Doly02/nxp-mcxn947-datalogger/application/doc/latex/task__switching_8h.tex

\doxysection{include/task\+\_\+switching.h File Reference}
\hypertarget{task__switching_8h}{}\label{task__switching_8h}\index{include/task\_switching.h@{include/task\_switching.h}}
{\ttfamily \#include "{}usb\+\_\+device\+\_\+dci.\+h"{}}\newline
\doxysubsubsection*{Functions}
\begin{DoxyCompactItemize}
\item 
usb\+\_\+device\+\_\+notification\+\_\+t \mbox{\hyperlink{task__switching_8h_ab4bb1b4063898f52aa390037fc37db81}{USB\+\_\+\+State}} (usb\+\_\+device\+\_\+struct\+\_\+t \texorpdfstring{$\ast$}{*}p\+Device\+Handle)
\begin{DoxyCompactList}\small\item\em Checks If Application USB Is Attached To Digital Data Logger. \end{DoxyCompactList}\end{DoxyCompactItemize}
\doxysubsubsection*{Variables}
\begin{DoxyCompactItemize}
\item 
usb\+\_\+msc\+\_\+struct\+\_\+t \mbox{\hyperlink{task__switching_8h_ae3a33b5a19fe04eeba3ebf4259f74625}{g\+\_\+msc}}
\begin{DoxyCompactList}\small\item\em Mass Storage Descriptor. \end{DoxyCompactList}\end{DoxyCompactItemize}

\doxysubsection{Function Documentation}
\Hypertarget{task__switching_8h_ab4bb1b4063898f52aa390037fc37db81}\index{task\_switching.h@{task\_switching.h}!USB\_State@{USB\_State}}
\index{USB\_State@{USB\_State}!task\_switching.h@{task\_switching.h}}
\doxysubsubsection{\texorpdfstring{USB\_State()}{USB\_State()}}
{\footnotesize\ttfamily \label{task__switching_8h_ab4bb1b4063898f52aa390037fc37db81} 
usb\+\_\+device\+\_\+notification\+\_\+t USB\+\_\+\+State (\begin{DoxyParamCaption}\item[{usb\+\_\+device\+\_\+struct\+\_\+t \texorpdfstring{$\ast$}{*}}]{p\+Device\+Handle}{}\end{DoxyParamCaption})}

Checks If Application USB Is Attached To Digital Data Logger. 

Checks Thru USB OTG (USB On-\/\+To-\/\+Go) SC Register. 
\begin{DoxyParams}[1]{Parameters}
\mbox{\texttt{ in}}  & {\em p\+Device\+Handle} & Pointer to USB Device Handle (e.\+g. Mass Storage Handle).\\
\hline
\end{DoxyParams}
\begin{DoxyReturn}{Returns}
k\+USB\+\_\+\+Device\+Notify\+Attach if USB Is Attached Otherwise Returns k\+USB\+\_\+\+Device\+Notify\+Detach. 
\end{DoxyReturn}

\doxysubsection{Variable Documentation}
\Hypertarget{task__switching_8h_ae3a33b5a19fe04eeba3ebf4259f74625}\index{task\_switching.h@{task\_switching.h}!g\_msc@{g\_msc}}
\index{g\_msc@{g\_msc}!task\_switching.h@{task\_switching.h}}
\doxysubsubsection{\texorpdfstring{g\_msc}{g\_msc}}
{\footnotesize\ttfamily \label{task__switching_8h_ae3a33b5a19fe04eeba3ebf4259f74625} 
usb\+\_\+msc\+\_\+struct\+\_\+t g\+\_\+msc\hspace{0.3cm}{\ttfamily [extern]}}

Mass Storage Descriptor. 

Mass Storage Descriptor.

MISRA Deviation\+: Rule 8.\+4 \mbox{[}Required\mbox{]} Suppress\+: External Object Has Definition Without Prior Declaration in This File. Justification\+: Declaration of \textquotesingle{}g\+\_\+msc\textquotesingle{} is intentionally placed in \textquotesingle{}\doxylink{app__tasks_8h}{app\+\_\+tasks.\+h}\textquotesingle{}, The Current File Only Provides The Definition.
