Doly02/nxp-mcxn947-datalogger/application/doc/latex/temperature_8c.tex

\doxysection{src/temperature.c File Reference}
\hypertarget{temperature_8c}{}\label{temperature_8c}\index{src/temperature.c@{src/temperature.c}}
{\ttfamily \#include $<$led.\+h$>$}\newline
{\ttfamily \#include "{}fsl\+\_\+debug\+\_\+console.\+h"{}}\newline
{\ttfamily \#include "{}fsl\+\_\+ctimer.\+h"{}}\newline
{\ttfamily \#include "{}temperature.\+h"{}}\newline
{\ttfamily \#include "{}defs.\+h"{}}\newline
\doxysubsubsection*{Macros}
\begin{DoxyCompactItemize}
\item 
\#define \mbox{\hyperlink{temperature_8c_afcaf37eb8fb30d41d86b119127cb9368}{LPI2\+C\+\_\+\+TX\+\_\+\+DMA\+\_\+\+CHANNEL}}~0\+UL
\begin{DoxyCompactList}\small\item\em I2C DMA Channel For Transmission. \end{DoxyCompactList}\item 
\#define \mbox{\hyperlink{temperature_8c_a1b99f71e2df43e2f7b57250dba60bc9a}{LPI2\+C\+\_\+\+RX\+\_\+\+DMA\+\_\+\+CHANNEL}}~1UL
\begin{DoxyCompactList}\small\item\em I2C DMA Channel For Reception. \end{DoxyCompactList}\item 
\#define \mbox{\hyperlink{temperature_8c_ae02f1575c21c401c357de6456cb0b472}{LPI2\+C\+\_\+\+TX\+\_\+\+CHANNEL}}~(int32\+\_\+t)k\+Dma1\+Request\+Mux\+Lp\+Flexcomm5\+Tx
\begin{DoxyCompactList}\small\item\em Connection Between DMA Channel 1 and LP\+\_\+\+FLEXCOMM5 Tx. \end{DoxyCompactList}\item 
\#define \mbox{\hyperlink{temperature_8c_aef436e53172ccba5c0370cc9e48d1989}{LPI2\+C\+\_\+\+RX\+\_\+\+EDMA\+\_\+\+CHANNEL}}~(int32\+\_\+t)k\+Dma1\+Request\+Mux\+Lp\+Flexcomm5\+Rx
\begin{DoxyCompactList}\small\item\em Connection Between DMA Channel 1 and LP\+\_\+\+FLEXCOMM5 Rx. \end{DoxyCompactList}\item 
\#define \mbox{\hyperlink{temperature_8c_a886f2dadbf959e761f53d4c0572158e7}{I2\+C\+\_\+\+MASTER\+\_\+\+I2\+C5}}~((LPI2\+C\+\_\+\+Type \texorpdfstring{$\ast$}{*})LPI2\+C5\+\_\+\+BASE)
\begin{DoxyCompactList}\small\item\em Points To I2C Peripheral Unit (Specifically LPI2\+C5 Instance). \end{DoxyCompactList}\item 
\#define \mbox{\hyperlink{temperature_8c_a9c2dd9164220c441449c70bade5baaf1}{P3\+T1755\+\_\+\+ADDR\+\_\+7\+BIT}}~0x48U
\begin{DoxyCompactList}\small\item\em I2C Address of P3\+T1755 Temperature Sensor. \end{DoxyCompactList}\item 
\#define \mbox{\hyperlink{temperature_8c_a31568ea8caf00a3ec699c01652c771d0}{I2\+C\+\_\+\+BAUDRATE}}~100000U
\begin{DoxyCompactList}\small\item\em Desired Baud Rate For I2C. \end{DoxyCompactList}\item 
\#define \mbox{\hyperlink{temperature_8c_a110741ac6782dd7e97d323608505dd1e}{PRINT\+\_\+\+REG\+\_\+\+OUTPUT}}~true
\begin{DoxyCompactList}\small\item\em Enables Printout of P3\+T1755 Register. \end{DoxyCompactList}\item 
\#define \mbox{\hyperlink{temperature_8c_a6c7cd32e1bac137f05e4a752b4ad10af}{BUFF\+\_\+\+SIZE}}~2
\begin{DoxyCompactList}\small\item\em Receive Buffer Size. \end{DoxyCompactList}\item 
\#define \mbox{\hyperlink{temperature_8c_a131b307523cbb7ad0b17a724115a5099}{REGISTER\+\_\+\+TEMPERATURE}}~0x00
\begin{DoxyCompactList}\small\item\em Temperature Register Address of P3\+T1755. \end{DoxyCompactList}\item 
\#define \mbox{\hyperlink{temperature_8c_a46f3492d1abbdaa8919cb57b94343daf}{REGISTER\+\_\+\+CONFIG}}~0x01
\begin{DoxyCompactList}\small\item\em Configuration Register Address of P3\+T1755. \end{DoxyCompactList}\item 
\#define \mbox{\hyperlink{temperature_8c_a31ab751e7975e20c85db034069d4353f}{REGISTER\+\_\+\+THVST}}~0x02
\item 
\#define \mbox{\hyperlink{temperature_8c_a9f4bd4fcf6e33727b5a85c258b8cbe1a}{REGISTER\+\_\+\+TOS}}~0x03
\end{DoxyCompactItemize}
\doxysubsubsection*{Functions}
\begin{DoxyCompactItemize}
\item 
\mbox{\hyperlink{temperature_8c_ab012c2d8730f13da3f0615ca9f93414d}{AT\+\_\+\+NONCACHEABLE\+\_\+\+SECTION}} (static uint8\+\_\+t g\+\_\+a\+Rx\+Buff\+\_\+\+I2\+C5\mbox{[}\mbox{\hyperlink{temperature_8c_a6c7cd32e1bac137f05e4a752b4ad10af}{BUFF\+\_\+\+SIZE}}\mbox{]})
\begin{DoxyCompactList}\small\item\em Reception Buffer. \end{DoxyCompactList}\item 
\mbox{\hyperlink{temperature_8c_a15897befedf315a0700d50b60b6d4bda}{AT\+\_\+\+NONCACHEABLE\+\_\+\+SECTION}} (static lpi2c\+\_\+master\+\_\+edma\+\_\+handle\+\_\+t g\+\_\+\+Edma\+Handle\+\_\+\+I2\+C5)
\begin{DoxyCompactList}\small\item\em e\+DMA Driver Handle Used For Non-\/\+Blocking DMA Transfer. \end{DoxyCompactList}\item 
static void \mbox{\hyperlink{temperature_8c_a038e5a1da8a787ae48b1e279cab6df55}{lpi2c\+\_\+callback}} (LPI2\+C\+\_\+\+Type \texorpdfstring{$\ast$}{*}base, lpi2c\+\_\+master\+\_\+edma\+\_\+handle\+\_\+t \texorpdfstring{$\ast$}{*}handle, status\+\_\+t status, void \texorpdfstring{$\ast$}{*}user\+Data)
\item 
void \mbox{\hyperlink{temperature_8c_a029ce7d1c3ffc8f1d357a6915fb7efc9}{CTIMER0\+\_\+\+IRQHandler}} (void)
\item 
uint8\+\_\+t \mbox{\hyperlink{temperature_8c_ad79223f453fb5cb3b14b0504b78c3b65}{Write}} (uint8\+\_\+t reg\+Address, uint8\+\_\+t val\mbox{[}$\,$\mbox{]})
\begin{DoxyCompactList}\small\item\em I2C Write Function. \end{DoxyCompactList}\item 
uint16\+\_\+t \mbox{\hyperlink{temperature_8c_af7ebaac8aebcb5a7b3147b378d4d1e82}{Read}} (uint8\+\_\+t reg\+Address)
\begin{DoxyCompactList}\small\item\em I2C Read Function. \end{DoxyCompactList}\item 
float \mbox{\hyperlink{temperature_8c_a0b017c2ac439a408d7b0d2bb07c2c3af}{TMP\+\_\+\+Get\+Temperature}} (void)
\begin{DoxyCompactList}\small\item\em Gets Temperature From On-\/\+Board P3\+T1755 Temperature Sensor. \end{DoxyCompactList}\item 
uint8\+\_\+t \mbox{\hyperlink{temperature_8c_a147cb7fa3ec99aa1038a20fd3d5ed0c3}{TMP\+\_\+\+Init}} (void)
\begin{DoxyCompactList}\small\item\em Initialize On-\/\+Board P3\+T1755 Temperature Sensor. \end{DoxyCompactList}\end{DoxyCompactItemize}
\doxysubsubsection*{Variables}
\begin{DoxyCompactItemize}
\item 
static edma\+\_\+handle\+\_\+t \mbox{\hyperlink{temperature_8c_a50fdd2b8d8084e9a4e600ae8af2f258a}{g\+\_\+\+Edma\+Tx\+Handle\+\_\+\+I2\+C5}}
\begin{DoxyCompactList}\small\item\em Tx e\+DMA Handle. \end{DoxyCompactList}\item 
static edma\+\_\+handle\+\_\+t \mbox{\hyperlink{temperature_8c_a776091829eca10175ea2ede27a31c45b}{g\+\_\+\+Edma\+Rx\+Handle\+\_\+\+I2\+C5}}
\begin{DoxyCompactList}\small\item\em Rx e\+DMA Handle. \end{DoxyCompactList}\item 
static volatile bool \mbox{\hyperlink{temperature_8c_a5c2a41bb43d5c3f97eaeff90195f16e0}{g\+\_\+b\+Completion\+Flag\+\_\+\+I2\+C5}} = false
\begin{DoxyCompactList}\small\item\em Flag Indicating Whether The Transfer Has Finished. \end{DoxyCompactList}\item 
static lpi2c\+\_\+master\+\_\+transfer\+\_\+t \mbox{\hyperlink{temperature_8c_a04223a52c21e3c74a057039cc4859680}{g\+\_\+\+Xfer\+\_\+\+I2\+C5}} = \{0\}
\end{DoxyCompactItemize}

\doxysubsection{Macro Definition Documentation}
\Hypertarget{temperature_8c_a6c7cd32e1bac137f05e4a752b4ad10af}\index{temperature.c@{temperature.c}!BUFF\_SIZE@{BUFF\_SIZE}}
\index{BUFF\_SIZE@{BUFF\_SIZE}!temperature.c@{temperature.c}}
\doxysubsubsection{\texorpdfstring{BUFF\_SIZE}{BUFF\_SIZE}}
{\footnotesize\ttfamily \label{temperature_8c_a6c7cd32e1bac137f05e4a752b4ad10af} 
\#define BUFF\+\_\+\+SIZE~2}

Receive Buffer Size. 

\Hypertarget{temperature_8c_a31568ea8caf00a3ec699c01652c771d0}\index{temperature.c@{temperature.c}!I2C\_BAUDRATE@{I2C\_BAUDRATE}}
\index{I2C\_BAUDRATE@{I2C\_BAUDRATE}!temperature.c@{temperature.c}}
\doxysubsubsection{\texorpdfstring{I2C\_BAUDRATE}{I2C\_BAUDRATE}}
{\footnotesize\ttfamily \label{temperature_8c_a31568ea8caf00a3ec699c01652c771d0} 
\#define I2\+C\+\_\+\+BAUDRATE~100000U}

Desired Baud Rate For I2C. 

Frequency -\/ 100k\+Hz. \Hypertarget{temperature_8c_a886f2dadbf959e761f53d4c0572158e7}\index{temperature.c@{temperature.c}!I2C\_MASTER\_I2C5@{I2C\_MASTER\_I2C5}}
\index{I2C\_MASTER\_I2C5@{I2C\_MASTER\_I2C5}!temperature.c@{temperature.c}}
\doxysubsubsection{\texorpdfstring{I2C\_MASTER\_I2C5}{I2C\_MASTER\_I2C5}}
{\footnotesize\ttfamily \label{temperature_8c_a886f2dadbf959e761f53d4c0572158e7} 
\#define I2\+C\+\_\+\+MASTER\+\_\+\+I2\+C5~((LPI2\+C\+\_\+\+Type \texorpdfstring{$\ast$}{*})LPI2\+C5\+\_\+\+BASE)}

Points To I2C Peripheral Unit (Specifically LPI2\+C5 Instance). 

\Hypertarget{temperature_8c_a1b99f71e2df43e2f7b57250dba60bc9a}\index{temperature.c@{temperature.c}!LPI2C\_RX\_DMA\_CHANNEL@{LPI2C\_RX\_DMA\_CHANNEL}}
\index{LPI2C\_RX\_DMA\_CHANNEL@{LPI2C\_RX\_DMA\_CHANNEL}!temperature.c@{temperature.c}}
\doxysubsubsection{\texorpdfstring{LPI2C\_RX\_DMA\_CHANNEL}{LPI2C\_RX\_DMA\_CHANNEL}}
{\footnotesize\ttfamily \label{temperature_8c_a1b99f71e2df43e2f7b57250dba60bc9a} 
\#define LPI2\+C\+\_\+\+RX\+\_\+\+DMA\+\_\+\+CHANNEL~1UL}

I2C DMA Channel For Reception. 

\Hypertarget{temperature_8c_aef436e53172ccba5c0370cc9e48d1989}\index{temperature.c@{temperature.c}!LPI2C\_RX\_EDMA\_CHANNEL@{LPI2C\_RX\_EDMA\_CHANNEL}}
\index{LPI2C\_RX\_EDMA\_CHANNEL@{LPI2C\_RX\_EDMA\_CHANNEL}!temperature.c@{temperature.c}}
\doxysubsubsection{\texorpdfstring{LPI2C\_RX\_EDMA\_CHANNEL}{LPI2C\_RX\_EDMA\_CHANNEL}}
{\footnotesize\ttfamily \label{temperature_8c_aef436e53172ccba5c0370cc9e48d1989} 
\#define LPI2\+C\+\_\+\+RX\+\_\+\+EDMA\+\_\+\+CHANNEL~(int32\+\_\+t)k\+Dma1\+Request\+Mux\+Lp\+Flexcomm5\+Rx}

Connection Between DMA Channel 1 and LP\+\_\+\+FLEXCOMM5 Rx. 

\Hypertarget{temperature_8c_ae02f1575c21c401c357de6456cb0b472}\index{temperature.c@{temperature.c}!LPI2C\_TX\_CHANNEL@{LPI2C\_TX\_CHANNEL}}
\index{LPI2C\_TX\_CHANNEL@{LPI2C\_TX\_CHANNEL}!temperature.c@{temperature.c}}
\doxysubsubsection{\texorpdfstring{LPI2C\_TX\_CHANNEL}{LPI2C\_TX\_CHANNEL}}
{\footnotesize\ttfamily \label{temperature_8c_ae02f1575c21c401c357de6456cb0b472} 
\#define LPI2\+C\+\_\+\+TX\+\_\+\+CHANNEL~(int32\+\_\+t)k\+Dma1\+Request\+Mux\+Lp\+Flexcomm5\+Tx}

Connection Between DMA Channel 1 and LP\+\_\+\+FLEXCOMM5 Tx. 

\Hypertarget{temperature_8c_afcaf37eb8fb30d41d86b119127cb9368}\index{temperature.c@{temperature.c}!LPI2C\_TX\_DMA\_CHANNEL@{LPI2C\_TX\_DMA\_CHANNEL}}
\index{LPI2C\_TX\_DMA\_CHANNEL@{LPI2C\_TX\_DMA\_CHANNEL}!temperature.c@{temperature.c}}
\doxysubsubsection{\texorpdfstring{LPI2C\_TX\_DMA\_CHANNEL}{LPI2C\_TX\_DMA\_CHANNEL}}
{\footnotesize\ttfamily \label{temperature_8c_afcaf37eb8fb30d41d86b119127cb9368} 
\#define LPI2\+C\+\_\+\+TX\+\_\+\+DMA\+\_\+\+CHANNEL~0\+UL}

I2C DMA Channel For Transmission. 

\Hypertarget{temperature_8c_a9c2dd9164220c441449c70bade5baaf1}\index{temperature.c@{temperature.c}!P3T1755\_ADDR\_7BIT@{P3T1755\_ADDR\_7BIT}}
\index{P3T1755\_ADDR\_7BIT@{P3T1755\_ADDR\_7BIT}!temperature.c@{temperature.c}}
\doxysubsubsection{\texorpdfstring{P3T1755\_ADDR\_7BIT}{P3T1755\_ADDR\_7BIT}}
{\footnotesize\ttfamily \label{temperature_8c_a9c2dd9164220c441449c70bade5baaf1} 
\#define P3\+T1755\+\_\+\+ADDR\+\_\+7\+BIT~0x48U}

I2C Address of P3\+T1755 Temperature Sensor. 

\Hypertarget{temperature_8c_a110741ac6782dd7e97d323608505dd1e}\index{temperature.c@{temperature.c}!PRINT\_REG\_OUTPUT@{PRINT\_REG\_OUTPUT}}
\index{PRINT\_REG\_OUTPUT@{PRINT\_REG\_OUTPUT}!temperature.c@{temperature.c}}
\doxysubsubsection{\texorpdfstring{PRINT\_REG\_OUTPUT}{PRINT\_REG\_OUTPUT}}
{\footnotesize\ttfamily \label{temperature_8c_a110741ac6782dd7e97d323608505dd1e} 
\#define PRINT\+\_\+\+REG\+\_\+\+OUTPUT~true}

Enables Printout of P3\+T1755 Register. 

\Hypertarget{temperature_8c_a46f3492d1abbdaa8919cb57b94343daf}\index{temperature.c@{temperature.c}!REGISTER\_CONFIG@{REGISTER\_CONFIG}}
\index{REGISTER\_CONFIG@{REGISTER\_CONFIG}!temperature.c@{temperature.c}}
\doxysubsubsection{\texorpdfstring{REGISTER\_CONFIG}{REGISTER\_CONFIG}}
{\footnotesize\ttfamily \label{temperature_8c_a46f3492d1abbdaa8919cb57b94343daf} 
\#define REGISTER\+\_\+\+CONFIG~0x01}

Configuration Register Address of P3\+T1755. 

\Hypertarget{temperature_8c_a131b307523cbb7ad0b17a724115a5099}\index{temperature.c@{temperature.c}!REGISTER\_TEMPERATURE@{REGISTER\_TEMPERATURE}}
\index{REGISTER\_TEMPERATURE@{REGISTER\_TEMPERATURE}!temperature.c@{temperature.c}}
\doxysubsubsection{\texorpdfstring{REGISTER\_TEMPERATURE}{REGISTER\_TEMPERATURE}}
{\footnotesize\ttfamily \label{temperature_8c_a131b307523cbb7ad0b17a724115a5099} 
\#define REGISTER\+\_\+\+TEMPERATURE~0x00}

Temperature Register Address of P3\+T1755. 

\Hypertarget{temperature_8c_a31ab751e7975e20c85db034069d4353f}\index{temperature.c@{temperature.c}!REGISTER\_THVST@{REGISTER\_THVST}}
\index{REGISTER\_THVST@{REGISTER\_THVST}!temperature.c@{temperature.c}}
\doxysubsubsection{\texorpdfstring{REGISTER\_THVST}{REGISTER\_THVST}}
{\footnotesize\ttfamily \label{temperature_8c_a31ab751e7975e20c85db034069d4353f} 
\#define REGISTER\+\_\+\+THVST~0x02}

\Hypertarget{temperature_8c_a9f4bd4fcf6e33727b5a85c258b8cbe1a}\index{temperature.c@{temperature.c}!REGISTER\_TOS@{REGISTER\_TOS}}
\index{REGISTER\_TOS@{REGISTER\_TOS}!temperature.c@{temperature.c}}
\doxysubsubsection{\texorpdfstring{REGISTER\_TOS}{REGISTER\_TOS}}
{\footnotesize\ttfamily \label{temperature_8c_a9f4bd4fcf6e33727b5a85c258b8cbe1a} 
\#define REGISTER\+\_\+\+TOS~0x03}

\doxysubsection{Function Documentation}
\Hypertarget{temperature_8c_a15897befedf315a0700d50b60b6d4bda}\index{temperature.c@{temperature.c}!AT\_NONCACHEABLE\_SECTION@{AT\_NONCACHEABLE\_SECTION}}
\index{AT\_NONCACHEABLE\_SECTION@{AT\_NONCACHEABLE\_SECTION}!temperature.c@{temperature.c}}
\doxysubsubsection{\texorpdfstring{AT\_NONCACHEABLE\_SECTION()}{AT\_NONCACHEABLE\_SECTION()}\hspace{0.1cm}{\footnotesize\ttfamily [1/2]}}
{\footnotesize\ttfamily \label{temperature_8c_a15897befedf315a0700d50b60b6d4bda} 
AT\+\_\+\+NONCACHEABLE\+\_\+\+SECTION (\begin{DoxyParamCaption}\item[{static lpi2c\+\_\+master\+\_\+edma\+\_\+handle\+\_\+t}]{g\+\_\+\+Edma\+Handle\+\_\+\+I2\+C5}{}\end{DoxyParamCaption})}

e\+DMA Driver Handle Used For Non-\/\+Blocking DMA Transfer. 

\Hypertarget{temperature_8c_ab012c2d8730f13da3f0615ca9f93414d}\index{temperature.c@{temperature.c}!AT\_NONCACHEABLE\_SECTION@{AT\_NONCACHEABLE\_SECTION}}
\index{AT\_NONCACHEABLE\_SECTION@{AT\_NONCACHEABLE\_SECTION}!temperature.c@{temperature.c}}
\doxysubsubsection{\texorpdfstring{AT\_NONCACHEABLE\_SECTION()}{AT\_NONCACHEABLE\_SECTION()}\hspace{0.1cm}{\footnotesize\ttfamily [2/2]}}
{\footnotesize\ttfamily \label{temperature_8c_ab012c2d8730f13da3f0615ca9f93414d} 
AT\+\_\+\+NONCACHEABLE\+\_\+\+SECTION (\begin{DoxyParamCaption}\item[{static uint8\+\_\+t}]{g\+\_\+a\+Rx\+Buff\+\_\+\+I2\+C5}{\mbox{[}\+BUFF\+\_\+\+SIZE\mbox{]}}\end{DoxyParamCaption})}

Reception Buffer. 

Must Be In Non-\/\+Cacheable Memory Due To Usage of DMA. \Hypertarget{temperature_8c_a029ce7d1c3ffc8f1d357a6915fb7efc9}\index{temperature.c@{temperature.c}!CTIMER0\_IRQHandler@{CTIMER0\_IRQHandler}}
\index{CTIMER0\_IRQHandler@{CTIMER0\_IRQHandler}!temperature.c@{temperature.c}}
\doxysubsubsection{\texorpdfstring{CTIMER0\_IRQHandler()}{CTIMER0\_IRQHandler()}}
{\footnotesize\ttfamily \label{temperature_8c_a029ce7d1c3ffc8f1d357a6915fb7efc9} 
void CTIMER0\+\_\+\+IRQHandler (\begin{DoxyParamCaption}\item[{void}]{}{}\end{DoxyParamCaption})}

\Hypertarget{temperature_8c_a038e5a1da8a787ae48b1e279cab6df55}\index{temperature.c@{temperature.c}!lpi2c\_callback@{lpi2c\_callback}}
\index{lpi2c\_callback@{lpi2c\_callback}!temperature.c@{temperature.c}}
\doxysubsubsection{\texorpdfstring{lpi2c\_callback()}{lpi2c\_callback()}}
{\footnotesize\ttfamily \label{temperature_8c_a038e5a1da8a787ae48b1e279cab6df55} 
static void lpi2c\+\_\+callback (\begin{DoxyParamCaption}\item[{LPI2\+C\+\_\+\+Type \texorpdfstring{$\ast$}{*}}]{base}{, }\item[{lpi2c\+\_\+master\+\_\+edma\+\_\+handle\+\_\+t \texorpdfstring{$\ast$}{*}}]{handle}{, }\item[{status\+\_\+t}]{status}{, }\item[{void \texorpdfstring{$\ast$}{*}}]{user\+Data}{}\end{DoxyParamCaption})\hspace{0.3cm}{\ttfamily [static]}}

\Hypertarget{temperature_8c_af7ebaac8aebcb5a7b3147b378d4d1e82}\index{temperature.c@{temperature.c}!Read@{Read}}
\index{Read@{Read}!temperature.c@{temperature.c}}
\doxysubsubsection{\texorpdfstring{Read()}{Read()}}
{\footnotesize\ttfamily \label{temperature_8c_af7ebaac8aebcb5a7b3147b378d4d1e82} 
uint16\+\_\+t Read (\begin{DoxyParamCaption}\item[{uint8\+\_\+t}]{reg\+Address}{}\end{DoxyParamCaption})}

I2C Read Function. 

\begin{DoxyParams}[1]{Parameters}
\mbox{\texttt{ in}}  & {\em reg\+Address} & Address of The Register From Which The Reading Will Take Place.\\
\hline
\end{DoxyParams}

\begin{DoxyRetVals}{Return values}
{\em Returns} & The Read Value From The Registry. \\
\hline
\end{DoxyRetVals}
\Hypertarget{temperature_8c_a0b017c2ac439a408d7b0d2bb07c2c3af}\index{temperature.c@{temperature.c}!TMP\_GetTemperature@{TMP\_GetTemperature}}
\index{TMP\_GetTemperature@{TMP\_GetTemperature}!temperature.c@{temperature.c}}
\doxysubsubsection{\texorpdfstring{TMP\_GetTemperature()}{TMP\_GetTemperature()}}
{\footnotesize\ttfamily \label{temperature_8c_a0b017c2ac439a408d7b0d2bb07c2c3af} 
float TMP\+\_\+\+Get\+Temperature (\begin{DoxyParamCaption}\item[{void}]{}{}\end{DoxyParamCaption})}

Gets Temperature From On-\/\+Board P3\+T1755 Temperature Sensor. 

\begin{DoxyRetVals}{Return values}
{\em Returns} & Temperature As Float Number. \\
\hline
\end{DoxyRetVals}
\Hypertarget{temperature_8c_a147cb7fa3ec99aa1038a20fd3d5ed0c3}\index{temperature.c@{temperature.c}!TMP\_Init@{TMP\_Init}}
\index{TMP\_Init@{TMP\_Init}!temperature.c@{temperature.c}}
\doxysubsubsection{\texorpdfstring{TMP\_Init()}{TMP\_Init()}}
{\footnotesize\ttfamily \label{temperature_8c_a147cb7fa3ec99aa1038a20fd3d5ed0c3} 
uint8\+\_\+t TMP\+\_\+\+Init (\begin{DoxyParamCaption}\item[{void}]{}{}\end{DoxyParamCaption})}

Initialize On-\/\+Board P3\+T1755 Temperature Sensor. 

\Hypertarget{temperature_8c_ad79223f453fb5cb3b14b0504b78c3b65}\index{temperature.c@{temperature.c}!Write@{Write}}
\index{Write@{Write}!temperature.c@{temperature.c}}
\doxysubsubsection{\texorpdfstring{Write()}{Write()}}
{\footnotesize\ttfamily \label{temperature_8c_ad79223f453fb5cb3b14b0504b78c3b65} 
uint8\+\_\+t Write (\begin{DoxyParamCaption}\item[{uint8\+\_\+t}]{reg\+Address}{, }\item[{uint8\+\_\+t}]{val}{\mbox{[}$\,$\mbox{]}}\end{DoxyParamCaption})}

I2C Write Function. 

\begin{DoxyParams}[1]{Parameters}
\mbox{\texttt{ in}}  & {\em reg\+Address} & Address of The Register To Be Written To. \\
\hline
\mbox{\texttt{ in}}  & {\em val} & Array of Values To Be Written To The Register.\\
\hline
\end{DoxyParams}

\begin{DoxyRetVals}{Return values}
{\em If} & The Write Succeeds, Returns 0. \\
\hline
\end{DoxyRetVals}

\doxysubsection{Variable Documentation}
\Hypertarget{temperature_8c_a5c2a41bb43d5c3f97eaeff90195f16e0}\index{temperature.c@{temperature.c}!g\_bCompletionFlag\_I2C5@{g\_bCompletionFlag\_I2C5}}
\index{g\_bCompletionFlag\_I2C5@{g\_bCompletionFlag\_I2C5}!temperature.c@{temperature.c}}
\doxysubsubsection{\texorpdfstring{g\_bCompletionFlag\_I2C5}{g\_bCompletionFlag\_I2C5}}
{\footnotesize\ttfamily \label{temperature_8c_a5c2a41bb43d5c3f97eaeff90195f16e0} 
volatile bool g\+\_\+b\+Completion\+Flag\+\_\+\+I2\+C5 = false\hspace{0.3cm}{\ttfamily [static]}}

Flag Indicating Whether The Transfer Has Finished. 

\Hypertarget{temperature_8c_a776091829eca10175ea2ede27a31c45b}\index{temperature.c@{temperature.c}!g\_EdmaRxHandle\_I2C5@{g\_EdmaRxHandle\_I2C5}}
\index{g\_EdmaRxHandle\_I2C5@{g\_EdmaRxHandle\_I2C5}!temperature.c@{temperature.c}}
\doxysubsubsection{\texorpdfstring{g\_EdmaRxHandle\_I2C5}{g\_EdmaRxHandle\_I2C5}}
{\footnotesize\ttfamily \label{temperature_8c_a776091829eca10175ea2ede27a31c45b} 
edma\+\_\+handle\+\_\+t g\+\_\+\+Edma\+Rx\+Handle\+\_\+\+I2\+C5\hspace{0.3cm}{\ttfamily [static]}}

Rx e\+DMA Handle. 

\Hypertarget{temperature_8c_a50fdd2b8d8084e9a4e600ae8af2f258a}\index{temperature.c@{temperature.c}!g\_EdmaTxHandle\_I2C5@{g\_EdmaTxHandle\_I2C5}}
\index{g\_EdmaTxHandle\_I2C5@{g\_EdmaTxHandle\_I2C5}!temperature.c@{temperature.c}}
\doxysubsubsection{\texorpdfstring{g\_EdmaTxHandle\_I2C5}{g\_EdmaTxHandle\_I2C5}}
{\footnotesize\ttfamily \label{temperature_8c_a50fdd2b8d8084e9a4e600ae8af2f258a} 
edma\+\_\+handle\+\_\+t g\+\_\+\+Edma\+Tx\+Handle\+\_\+\+I2\+C5\hspace{0.3cm}{\ttfamily [static]}}

Tx e\+DMA Handle. 

\Hypertarget{temperature_8c_a04223a52c21e3c74a057039cc4859680}\index{temperature.c@{temperature.c}!g\_Xfer\_I2C5@{g\_Xfer\_I2C5}}
\index{g\_Xfer\_I2C5@{g\_Xfer\_I2C5}!temperature.c@{temperature.c}}
\doxysubsubsection{\texorpdfstring{g\_Xfer\_I2C5}{g\_Xfer\_I2C5}}
{\footnotesize\ttfamily \label{temperature_8c_a04223a52c21e3c74a057039cc4859680} 
lpi2c\+\_\+master\+\_\+transfer\+\_\+t g\+\_\+\+Xfer\+\_\+\+I2\+C5 = \{0\}\hspace{0.3cm}{\ttfamily [static]}}
