Doly02/nxp-mcxn947-datalogger/application/doc/latex/uart_8h_source.tex

\doxysection{uart.\+h}
\hypertarget{uart_8h_source}{}\label{uart_8h_source}\index{include/uart.h@{include/uart.h}}
\mbox{\hyperlink{uart_8h}{Go to the documentation of this file.}}
\begin{DoxyCode}{0}
\DoxyCodeLine{00001\ \textcolor{comment}{/******************************}}
\DoxyCodeLine{00002\ \textcolor{comment}{\ *\ \ Project:\ \ \ \ \ \ \ \ NXP\ MCXN947\ Datalogger}}
\DoxyCodeLine{00003\ \textcolor{comment}{\ *\ \ File\ Name:\ \ \ \ \ \ uart.h}}
\DoxyCodeLine{00004\ \textcolor{comment}{\ *\ \ Author:\ \ \ \ \ \ \ \ \ Tomas\ Dolak}}
\DoxyCodeLine{00005\ \textcolor{comment}{\ *\ \ Date:\ \ \ \ \ \ \ \ \ \ \ 25.11.2024}}
\DoxyCodeLine{00006\ \textcolor{comment}{\ *\ \ Description:\ \ \ \ Header\ File\ For\ The\ UART\ Peripheral\ Support.}}
\DoxyCodeLine{00007\ \textcolor{comment}{\ *}}
\DoxyCodeLine{00008\ \textcolor{comment}{\ *\ ****************************/}}
\DoxyCodeLine{00009\ }
\DoxyCodeLine{00010\ \textcolor{comment}{/******************************}}
\DoxyCodeLine{00011\ \textcolor{comment}{\ *\ \ @package\ \ \ \ \ \ \ \ NXP\ MCXN947\ Datalogger}}
\DoxyCodeLine{00012\ \textcolor{comment}{\ *\ \ @file\ \ \ \ \ \ \ \ \ \ \ uart.h}}
\DoxyCodeLine{00013\ \textcolor{comment}{\ *\ \ @author\ \ \ \ \ \ \ \ \ Tomas\ Dolak}}
\DoxyCodeLine{00014\ \textcolor{comment}{\ *\ \ @date\ \ \ \ \ \ \ \ \ \ \ 25.11.2024}}
\DoxyCodeLine{00015\ \textcolor{comment}{\ *\ \ @brief\ \ \ \ \ \ \ \ \ \ Header\ File\ For\ The\ UART\ Peripheral\ Support.}}
\DoxyCodeLine{00016\ \textcolor{comment}{\ *\ ****************************/}}
\DoxyCodeLine{00017\ }
\DoxyCodeLine{00018\ \textcolor{preprocessor}{\#ifndef\ UART\_H\_}}
\DoxyCodeLine{00019\ \textcolor{preprocessor}{\#define\ UART\_H\_}}
\DoxyCodeLine{00020\ }
\DoxyCodeLine{00021\ \textcolor{comment}{/*******************************************************************************}}
\DoxyCodeLine{00022\ \textcolor{comment}{\ *\ Includes}}
\DoxyCodeLine{00023\ \textcolor{comment}{\ ******************************************************************************/}}
\DoxyCodeLine{00024\ \textcolor{preprocessor}{\#include\ "{}pin\_mux.h"{}}}
\DoxyCodeLine{00025\ \textcolor{preprocessor}{\#include\ "{}clock\_config.h"{}}}
\DoxyCodeLine{00026\ \textcolor{preprocessor}{\#include\ "{}board.h"{}}}
\DoxyCodeLine{00027\ \textcolor{preprocessor}{\#include\ "{}fsl\_lpuart.h"{}}}
\DoxyCodeLine{00028\ }
\DoxyCodeLine{00029\ \textcolor{preprocessor}{\#include\ "{}fsl\_debug\_console.h"{}}}
\DoxyCodeLine{00030\ \textcolor{preprocessor}{\#include\ "{}fsl\_clock.h"{}}}
\DoxyCodeLine{00031\ \textcolor{comment}{/*******************************************************************************}}
\DoxyCodeLine{00032\ \textcolor{comment}{\ *\ Definitions}}
\DoxyCodeLine{00033\ \textcolor{comment}{\ ******************************************************************************/}}
\DoxyCodeLine{00037\ \textcolor{preprocessor}{\#define\ LPUART3\_CLK\_FREQ\ \ \ CLOCK\_GetLPFlexCommClkFreq(3u)}}
\DoxyCodeLine{00038\ }
\DoxyCodeLine{00039\ }
\DoxyCodeLine{00040\ \textcolor{comment}{/*******************************************************************************}}
\DoxyCodeLine{00041\ \textcolor{comment}{\ *\ Declarations}}
\DoxyCodeLine{00042\ \textcolor{comment}{\ ******************************************************************************/}}
\DoxyCodeLine{00043\ }
\DoxyCodeLine{00047\ \textcolor{keywordtype}{void}\ \mbox{\hyperlink{uart_8h_ad6f6f2234554d7faf55db52b66f45bc5}{UART\_Init}}(uint32\_t\ baudrate);}
\DoxyCodeLine{00048\ }
\DoxyCodeLine{00054\ \textcolor{keywordtype}{void}\ \mbox{\hyperlink{uart_8h_a6ee3953aba06a9d3e1695bb3ba147c18}{UART\_Print}}(uint8\_t\ ch);}
\DoxyCodeLine{00055\ }
\DoxyCodeLine{00059\ \textcolor{keywordtype}{void}\ \mbox{\hyperlink{uart_8h_ae2d34afb9a8bd33f0229eb6b34c57df2}{UART\_Enable}}(\textcolor{keywordtype}{void});}
\DoxyCodeLine{00060\ }
\DoxyCodeLine{00064\ \textcolor{keywordtype}{void}\ \mbox{\hyperlink{uart_8h_a76482cf7e9eb69dba68afd26b53b7f37}{UART\_Disable}}(\textcolor{keywordtype}{void});}
\DoxyCodeLine{00065\ }
\DoxyCodeLine{00070\ \textcolor{keywordtype}{void}\ \mbox{\hyperlink{uart_8h_a28f24a41744d2b956de47ae6318d9c05}{UART\_Deinit}}(\textcolor{keywordtype}{void});}
\DoxyCodeLine{00071\ }
\DoxyCodeLine{00072\ \textcolor{preprocessor}{\#endif\ }\textcolor{comment}{/*\ UART\_H\_\ */}\textcolor{preprocessor}{}}
\DoxyCodeLine{00073\ }

\end{DoxyCode}
