Doly02/nxp-mcxn947-datalogger/application/doc/latex/record_8c.tex

\doxysection{src/record.c File Reference}
\hypertarget{record_8c}{}\label{record_8c}\index{src/record.c@{src/record.c}}
{\ttfamily \#include $<$record.\+h$>$}\newline
{\ttfamily \#include "{}fsl\+\_\+irtc.\+h"{}}\newline
{\ttfamily \#include $<$limits.\+h$>$}\newline
\doxysubsubsection*{Macros}
\begin{DoxyCompactItemize}
\item 
\#define \mbox{\hyperlink{record_8c_a501f5c21d6fe4e60dc984cdaba5e892f}{CIRCULAR\+\_\+\+BUFFER\+\_\+\+SIZE}}~1024U
\begin{DoxyCompactList}\small\item\em Software FIFO Size. \end{DoxyCompactList}\item 
\#define \mbox{\hyperlink{record_8c_ad51ded0bbd705f02f73fc60c0b721ced}{BLOCK\+\_\+\+SIZE}}~512U
\begin{DoxyCompactList}\small\item\em Block Size For Write To SDHC Card Operation (In Bytes). \end{DoxyCompactList}\item 
\#define \mbox{\hyperlink{record_8c_ad7a1f4fbbe0adc28faeb0c657fa33cc4}{GET\+\_\+\+WAIT\+\_\+\+INTERVAL}}(seconds)
\begin{DoxyCompactList}\small\item\em Convert Time In Seconds To Number of Ticks. \end{DoxyCompactList}\item 
\#define \mbox{\hyperlink{record_8c_af91d15f16fa008fb2ea0436199bb2ab2}{GET\+\_\+\+CURRENT\+\_\+\+TIME\+\_\+\+MS}}()
\end{DoxyCompactItemize}
\doxysubsubsection*{Functions}
\begin{DoxyCompactItemize}
\item 
\mbox{\hyperlink{group___recording_ga1aa9629f7ba12059f55915fdfef8f6d7}{SDK\+\_\+\+ALIGN}} (static uint8\+\_\+t g\+\_\+au8\+Dma\+Buffer1\mbox{[}\mbox{\hyperlink{record_8c_ad51ded0bbd705f02f73fc60c0b721ced}{BLOCK\+\_\+\+SIZE}}\mbox{]}, BOARD\+\_\+\+SDMMC\+\_\+\+DATA\+\_\+\+BUFFER\+\_\+\+ALIGN\+\_\+\+SIZE)
\begin{DoxyCompactList}\small\item\em Buffer For Multi-\/\+Buffering -\/ In Particular Dual-\/\+Buffering, One Is Always Filled, The Other Is Processed. \end{DoxyCompactList}\item 
\mbox{\hyperlink{group___u_a_r_t_ga0f85dbf0cf3882e0ac219ed036b7e5df}{SDK\+\_\+\+ALIGN}} (static volatile uint8\+\_\+t g\+\_\+au8\+Circ\+Buffer\mbox{[}\mbox{\hyperlink{record_8c_a501f5c21d6fe4e60dc984cdaba5e892f}{CIRCULAR\+\_\+\+BUFFER\+\_\+\+SIZE}}\mbox{]}, BOARD\+\_\+\+SDMMC\+\_\+\+DATA\+\_\+\+BUFFER\+\_\+\+ALIGN\+\_\+\+SIZE)
\begin{DoxyCompactList}\small\item\em Circular Buffer For Reception of Data From UART Interrupt Service Routine. \end{DoxyCompactList}\item 
void \mbox{\hyperlink{record_8c_aac632a55c01036580b0f0f2521de688b}{LP\+\_\+\+FLEXCOMM3\+\_\+\+IRQHandler}} (void)
\begin{DoxyCompactList}\small\item\em LPUART3 IRQ Handler. \end{DoxyCompactList}\item 
DWORD \mbox{\hyperlink{record_8c_af58b536abfd30f77213f4ecaf2ac52f5}{get\+\_\+fattime}} (void)
\item 
uint32\+\_\+t \mbox{\hyperlink{record_8c_a68675110803994cd2f323d7b5ec22204}{CONSOLELOG\+\_\+\+Get\+Free\+Space\+MB}} (void)
\begin{DoxyCompactList}\small\item\em Gets Free Space on SD Card. \end{DoxyCompactList}\item 
\mbox{\hyperlink{error_8h_aeaf3178f631e362a9238a50fcdcaa039}{error\+\_\+t}} \mbox{\hyperlink{record_8c_a023ab61eb71b7b74e227c7347196791e}{CONSOLELOG\+\_\+\+Create\+File}} (void)
\begin{DoxyCompactList}\small\item\em Creates File Based Actual Date and Counter Value. \end{DoxyCompactList}\item 
\mbox{\hyperlink{error_8h_aeaf3178f631e362a9238a50fcdcaa039}{error\+\_\+t}} \mbox{\hyperlink{record_8c_ac1fa0a8fc8347a2972c4eb356d002b43}{CONSOLELOG\+\_\+\+Create\+Directory}} (void)
\begin{DoxyCompactList}\small\item\em Creates Directory Based Actual Date. \end{DoxyCompactList}\item 
uint32\+\_\+t \mbox{\hyperlink{record_8c_a956fc952a186ae09ce21409b7354cde7}{CONSOLELOG\+\_\+\+Get\+Transfered\+Bytes}} (void)
\begin{DoxyCompactList}\small\item\em Returns Currently Received Bytes Between LED Blinking. \end{DoxyCompactList}\item 
bool \mbox{\hyperlink{record_8c_af54d270ec7ba86c38b2903c41eca3676}{CONSOLELOG\+\_\+\+Get\+Flush\+Completed}} (void)
\begin{DoxyCompactList}\small\item\em Returns If Flush Was Completed or Not. \end{DoxyCompactList}\item 
void \mbox{\hyperlink{record_8c_a52b8002dd4c2a6b13860c0a0cf52a0a8}{CONSOLELOG\+\_\+\+Clear\+Transfered\+Bytes}} (void)
\begin{DoxyCompactList}\small\item\em Clears Currently Received Bytes After LED Blinking. \end{DoxyCompactList}\item 
FRESULT \mbox{\hyperlink{record_8c_a7569eaf79c91368fad87f25507fb8614}{CONSOLELOG\+\_\+\+Check\+File\+System}} (void)
\begin{DoxyCompactList}\small\item\em Checks If The File System Is Initialized. \end{DoxyCompactList}\item 
\mbox{\hyperlink{error_8h_aeaf3178f631e362a9238a50fcdcaa039}{error\+\_\+t}} \mbox{\hyperlink{record_8c_a7c874f2c9b56aa801cf2bee5565975f1}{CONSOLELOG\+\_\+\+Init}} (void)
\begin{DoxyCompactList}\small\item\em Initializes The Recording System and Mounts The File System. \end{DoxyCompactList}\item 
\mbox{\hyperlink{error_8h_aeaf3178f631e362a9238a50fcdcaa039}{error\+\_\+t}} \mbox{\hyperlink{record_8c_a79da7903033034cac5a75923611657f6}{CONSOLELOG\+\_\+\+Recording}} (uint32\+\_\+t file\+\_\+size)
\begin{DoxyCompactList}\small\item\em Starts The Recording Process by Initializing the File System, Creating a Directory, and Writing to a File. \end{DoxyCompactList}\item 
\mbox{\hyperlink{error_8h_aeaf3178f631e362a9238a50fcdcaa039}{error\+\_\+t}} \mbox{\hyperlink{record_8c_ae36046c53443afa593218c41f4b834fa}{CONSOLELOG\+\_\+\+Flush}} (void)
\begin{DoxyCompactList}\small\item\em Flushes Collected Data To The File If No Other Data Have Been Received By The Time Specified By TIMEOUT Macro. \end{DoxyCompactList}\item 
\mbox{\hyperlink{error_8h_aeaf3178f631e362a9238a50fcdcaa039}{error\+\_\+t}} \mbox{\hyperlink{record_8c_a91b1773f5158d67d12e9c6d40394b841}{CONSOLELOG\+\_\+\+Power\+Loss\+Flush}} (void)
\begin{DoxyCompactList}\small\item\em Flushes Collected Data To The File If Power Loss Was Detected. \end{DoxyCompactList}\item 
\mbox{\hyperlink{error_8h_aeaf3178f631e362a9238a50fcdcaa039}{error\+\_\+t}} \mbox{\hyperlink{record_8c_a310ec37130ed3dad88f57c14e72a3ed7}{CONSOLELOG\+\_\+\+Deinit}} (void)
\begin{DoxyCompactList}\small\item\em De-\/\+Initializes The Recording System and Un-\/\+Mounts The File System. \end{DoxyCompactList}\item 
\mbox{\hyperlink{error_8h_aeaf3178f631e362a9238a50fcdcaa039}{error\+\_\+t}} \mbox{\hyperlink{record_8c_af2718c8ac24b83f237cbd1dc970af06d}{CONSOLELOG\+\_\+\+Read\+Config}} (void)
\begin{DoxyCompactList}\small\item\em Reads and Processes The Configuration File From The Root directory. \end{DoxyCompactList}\item 
\mbox{\hyperlink{error_8h_aeaf3178f631e362a9238a50fcdcaa039}{error\+\_\+t}} \mbox{\hyperlink{record_8c_aeb7fb616b1f69f6cf4903a6058da06df}{CONSOLELOG\+\_\+\+Proccess\+Config\+File}} (const char \texorpdfstring{$\ast$}{*}content)
\begin{DoxyCompactList}\small\item\em Processes The Content of The Configuration File To Extract and Validate The Baudrate. \end{DoxyCompactList}\end{DoxyCompactItemize}
\doxysubsubsection*{Variables}
\begin{DoxyCompactItemize}
\item 
static FATFS \mbox{\hyperlink{group___recording_ga813e21877b77fc983a281279de3d13d8}{g\+\_\+file\+System}}
\begin{DoxyCompactList}\small\item\em File System Object. \end{DoxyCompactList}\item 
static FIL \mbox{\hyperlink{group___recording_ga6849136fb10da44df5884df6fc59588a}{g\+\_\+file\+Object}}
\begin{DoxyCompactList}\small\item\em File Object. \end{DoxyCompactList}\item 
static char \mbox{\hyperlink{group___recording_gac9f309262ccd3839f7daf0ba73be5005}{g\+\_\+u8\+Current\+Directory}} \mbox{[}32\mbox{]}
\begin{DoxyCompactList}\small\item\em Name Of The Folder Where The Files (Logs) From The Current Session Are Stored. \end{DoxyCompactList}\item 
static uint8\+\_\+t \texorpdfstring{$\ast$}{*} \mbox{\hyperlink{group___recording_gaac8be9babbe2654b3629e766c0b5e0b2}{g\+\_\+pu8\+Back\+Dma\+Buffer}} = g\+\_\+au8\+Dma\+Buffer1
\begin{DoxyCompactList}\small\item\em Back Buffer Which Serves For Data Collection From Circular Buffer And Is Used For Data-\/\+Processing (Time Stamps Are Inserted To This Buffer). \end{DoxyCompactList}\item 
static uint8\+\_\+t \texorpdfstring{$\ast$}{*} \mbox{\hyperlink{group___recording_ga6942269ddc23abb31caea237f570fc3e}{g\+\_\+pu8\+Front\+Dma\+Buffer}} = NULL
\begin{DoxyCompactList}\small\item\em Front Buffer Which Serves For Storing Data Into SD Card. \end{DoxyCompactList}\item 
static uint16\+\_\+t \mbox{\hyperlink{group___recording_ga7beba7dc88a1ae7ae1935202b9c001ae}{g\+\_\+u16\+Back\+Dma\+Buffer\+Idx}} = 0
\begin{DoxyCompactList}\small\item\em Pointer on Current Back DMA Buffer Into Which The Time Stamps Are Inserted. \end{DoxyCompactList}\item 
static bool \mbox{\hyperlink{group___recording_gae04fc0a92699c2a249e59d827e037af9}{g\+\_\+b\+Back\+Dma\+Buffer\+Ready}} = false
\begin{DoxyCompactList}\small\item\em Indicates That Collection Buffer (Back Buffer) Is Full and Ready To Swap. \end{DoxyCompactList}\item 
static Tick\+Type\+\_\+t \mbox{\hyperlink{group___recording_gab2133044474cb4d2b64febf2ef430513}{g\+\_\+last\+Data\+Tick}} = 0
\begin{DoxyCompactList}\small\item\em Value of Ticks When Last Character Was Received Thru LPUART. \end{DoxyCompactList}\item 
static uint32\+\_\+t \mbox{\hyperlink{group___recording_ga917ee1380772be61cefe6eb15f9b51dd}{g\+\_\+u32\+Current\+File\+Size}} = 0
\begin{DoxyCompactList}\small\item\em Tracks Current File Size. \end{DoxyCompactList}\item 
static uint16\+\_\+t \mbox{\hyperlink{group___recording_ga94090c10cebe28b90ec006581b06c0e5}{g\+\_\+u32\+File\+Counter}} = 1
\begin{DoxyCompactList}\small\item\em Counter For Unique File Names. \end{DoxyCompactList}\item 
static bool \mbox{\hyperlink{group___recording_gafff17b721dd91f02d491dd4823fa38bb}{g\+\_\+b\+Flush\+Completed}} = false
\begin{DoxyCompactList}\small\item\em Flush Completed Flag. \end{DoxyCompactList}\item 
static uint32\+\_\+t \mbox{\hyperlink{group___recording_ga56b2e93f80714c04880fd4c55b4395de}{g\+\_\+u32\+Bytes\+Transfered}} = 0U
\begin{DoxyCompactList}\small\item\em Transferred Bytes Between Blinking LEDs. \end{DoxyCompactList}\item 
static volatile uint32\+\_\+t \mbox{\hyperlink{group___u_a_r_t_ga4f4eced93ae5dcb56588db472d653230}{g\+\_\+u32\+Write\+Index}} = 0
\begin{DoxyCompactList}\small\item\em Index For Writing Into FIFO. \end{DoxyCompactList}\item 
static volatile uint32\+\_\+t \mbox{\hyperlink{group___u_a_r_t_ga0d9f0760ea8067a59144a9de9a20872e}{g\+\_\+u32\+Read\+Index}} = 0
\begin{DoxyCompactList}\small\item\em Index For Reading From FIFO. \end{DoxyCompactList}\end{DoxyCompactItemize}

\doxysubsection{Macro Definition Documentation}
\Hypertarget{record_8c_ad51ded0bbd705f02f73fc60c0b721ced}\index{record.c@{record.c}!BLOCK\_SIZE@{BLOCK\_SIZE}}
\index{BLOCK\_SIZE@{BLOCK\_SIZE}!record.c@{record.c}}
\doxysubsubsection{\texorpdfstring{BLOCK\_SIZE}{BLOCK\_SIZE}}
{\footnotesize\ttfamily \label{record_8c_ad51ded0bbd705f02f73fc60c0b721ced} 
\#define BLOCK\+\_\+\+SIZE~512U}

Block Size For Write To SDHC Card Operation (In Bytes). 

\Hypertarget{record_8c_a501f5c21d6fe4e60dc984cdaba5e892f}\index{record.c@{record.c}!CIRCULAR\_BUFFER\_SIZE@{CIRCULAR\_BUFFER\_SIZE}}
\index{CIRCULAR\_BUFFER\_SIZE@{CIRCULAR\_BUFFER\_SIZE}!record.c@{record.c}}
\doxysubsubsection{\texorpdfstring{CIRCULAR\_BUFFER\_SIZE}{CIRCULAR\_BUFFER\_SIZE}}
{\footnotesize\ttfamily \label{record_8c_a501f5c21d6fe4e60dc984cdaba5e892f} 
\#define CIRCULAR\+\_\+\+BUFFER\+\_\+\+SIZE~1024U}

Software FIFO Size. 

\Hypertarget{record_8c_af91d15f16fa008fb2ea0436199bb2ab2}\index{record.c@{record.c}!GET\_CURRENT\_TIME\_MS@{GET\_CURRENT\_TIME\_MS}}
\index{GET\_CURRENT\_TIME\_MS@{GET\_CURRENT\_TIME\_MS}!record.c@{record.c}}
\doxysubsubsection{\texorpdfstring{GET\_CURRENT\_TIME\_MS}{GET\_CURRENT\_TIME\_MS}}
{\footnotesize\ttfamily \label{record_8c_af91d15f16fa008fb2ea0436199bb2ab2} 
\#define GET\+\_\+\+CURRENT\+\_\+\+TIME\+\_\+\+MS(\begin{DoxyParamCaption}{}{}\end{DoxyParamCaption})}

{\bfseries Value\+:}
\begin{DoxyCode}{0}
\DoxyCodeLine{(xTaskGetTickCount()\ *\ portTICK\_PERIOD\_MS)}

\end{DoxyCode}
\Hypertarget{record_8c_ad7a1f4fbbe0adc28faeb0c657fa33cc4}\index{record.c@{record.c}!GET\_WAIT\_INTERVAL@{GET\_WAIT\_INTERVAL}}
\index{GET\_WAIT\_INTERVAL@{GET\_WAIT\_INTERVAL}!record.c@{record.c}}
\doxysubsubsection{\texorpdfstring{GET\_WAIT\_INTERVAL}{GET\_WAIT\_INTERVAL}}
{\footnotesize\ttfamily \label{record_8c_ad7a1f4fbbe0adc28faeb0c657fa33cc4} 
\#define GET\+\_\+\+WAIT\+\_\+\+INTERVAL(\begin{DoxyParamCaption}\item[{}]{seconds}{}\end{DoxyParamCaption})}

{\bfseries Value\+:}
\begin{DoxyCode}{0}
\DoxyCodeLine{((seconds)\ *\ 1000\ /\ configTICK\_RATE\_HZ)}

\end{DoxyCode}

Convert Time In Seconds To Number of Ticks. 

\begin{DoxyParams}{Parameters}
{\em seconds} & Number of Seconds To Transfer. \\
\hline
\end{DoxyParams}
\begin{DoxyReturn}{Returns}
Number of Ticks Corresponding To The Specified Number of Seconds. 
\end{DoxyReturn}

\doxysubsection{Function Documentation}
\Hypertarget{record_8c_a7569eaf79c91368fad87f25507fb8614}\index{record.c@{record.c}!CONSOLELOG\_CheckFileSystem@{CONSOLELOG\_CheckFileSystem}}
\index{CONSOLELOG\_CheckFileSystem@{CONSOLELOG\_CheckFileSystem}!record.c@{record.c}}
\doxysubsubsection{\texorpdfstring{CONSOLELOG\_CheckFileSystem()}{CONSOLELOG\_CheckFileSystem()}}
{\footnotesize\ttfamily \label{record_8c_a7569eaf79c91368fad87f25507fb8614} 
FRESULT CONSOLELOG\+\_\+\+Check\+File\+System (\begin{DoxyParamCaption}\item[{void}]{}{}\end{DoxyParamCaption})}

Checks If The File System Is Initialized. 

return F\+\_\+\+OK If File System Initialized. \Hypertarget{record_8c_a52b8002dd4c2a6b13860c0a0cf52a0a8}\index{record.c@{record.c}!CONSOLELOG\_ClearTransferedBytes@{CONSOLELOG\_ClearTransferedBytes}}
\index{CONSOLELOG\_ClearTransferedBytes@{CONSOLELOG\_ClearTransferedBytes}!record.c@{record.c}}
\doxysubsubsection{\texorpdfstring{CONSOLELOG\_ClearTransferedBytes()}{CONSOLELOG\_ClearTransferedBytes()}}
{\footnotesize\ttfamily \label{record_8c_a52b8002dd4c2a6b13860c0a0cf52a0a8} 
void CONSOLELOG\+\_\+\+Clear\+Transfered\+Bytes (\begin{DoxyParamCaption}\item[{void}]{}{}\end{DoxyParamCaption})}

Clears Currently Received Bytes After LED Blinking. 

\Hypertarget{record_8c_ac1fa0a8fc8347a2972c4eb356d002b43}\index{record.c@{record.c}!CONSOLELOG\_CreateDirectory@{CONSOLELOG\_CreateDirectory}}
\index{CONSOLELOG\_CreateDirectory@{CONSOLELOG\_CreateDirectory}!record.c@{record.c}}
\doxysubsubsection{\texorpdfstring{CONSOLELOG\_CreateDirectory()}{CONSOLELOG\_CreateDirectory()}}
{\footnotesize\ttfamily \label{record_8c_ac1fa0a8fc8347a2972c4eb356d002b43} 
\mbox{\hyperlink{error_8h_aeaf3178f631e362a9238a50fcdcaa039}{error\+\_\+t}} CONSOLELOG\+\_\+\+Create\+Directory (\begin{DoxyParamCaption}\item[{void}]{}{}\end{DoxyParamCaption})}

Creates Directory Based Actual Date. 

\begin{DoxyReturn}{Returns}
Returns Zero If Directory Creation Succeeded. 
\end{DoxyReturn}
MISRA Deviation\+: Rule 21.\+6 \mbox{[}Advisory\mbox{]} Suppress\+: Use Of Standard Library Function \textquotesingle{}snprintf()\textquotesingle{} Which Is Not Fully Bounded In All Environments. Justification\+: The Use Of \textquotesingle{}snprintf()\textquotesingle{} Is Intentional And Acceptable In This Context, The Format String And All Input Values Are Controlled and Predictable.

MISRA Deviation\+: Rule 21.\+6 \mbox{[}Advisory\mbox{]} Suppress\+: Use Of Standard Library Function \textquotesingle{}snprintf()\textquotesingle{} Which Is Not Fully Bounded In All Environments. Justification\+: The Use Of \textquotesingle{}snprintf()\textquotesingle{} Is Intentional And Acceptable In This Context, The Format String And All Input Values Are Controlled and Predictable.\Hypertarget{record_8c_a023ab61eb71b7b74e227c7347196791e}\index{record.c@{record.c}!CONSOLELOG\_CreateFile@{CONSOLELOG\_CreateFile}}
\index{CONSOLELOG\_CreateFile@{CONSOLELOG\_CreateFile}!record.c@{record.c}}
\doxysubsubsection{\texorpdfstring{CONSOLELOG\_CreateFile()}{CONSOLELOG\_CreateFile()}}
{\footnotesize\ttfamily \label{record_8c_a023ab61eb71b7b74e227c7347196791e} 
\mbox{\hyperlink{error_8h_aeaf3178f631e362a9238a50fcdcaa039}{error\+\_\+t}} CONSOLELOG\+\_\+\+Create\+File (\begin{DoxyParamCaption}\item[{void}]{}{}\end{DoxyParamCaption})}

Creates File Based Actual Date and Counter Value. 

\begin{DoxyReturn}{Returns}
Returns Zero If File Creation Succeeded. 
\end{DoxyReturn}
MISRA Deviation\+: Rule 21.\+6 Suppress\+: Use Of Standard Library Function \textquotesingle{}Snprintf\textquotesingle{}. Justification\+: \textquotesingle{}Snprintf\textquotesingle{} Is Deprecated But There Is No Better Equivalent For Safe String Formatting.

MISRA Deviation\+: Rule 10.\+1 \mbox{[}Required\mbox{]} Suppress\+: Bitwise Operation on Composite Constant Expression. Justification\+: FA\+\_\+\+WRITE and FA\+\_\+\+CREATE\+\_\+\+ALWAYS are Standard Bitmask Flags Defined By The Fat\+Fs Library. These Constants Are Designed To Be Combined Using Bitwise OR, and The Use is Safe and Intentional.

MISRA Deviation Note\+: The Following Expression is Intentionally Written in a Compact and Readable Form For Setting FAT File Time Stamps. All Shifts and Bitwise Operations Are Used Correctly, Even Though They Trigger MISRA Rule 10.\+1, 10.\+3, 10.\+4, 10.\+7, 12.\+2 Warnings. These are Suppressed Here For Clarity and Maintainability.\Hypertarget{record_8c_a310ec37130ed3dad88f57c14e72a3ed7}\index{record.c@{record.c}!CONSOLELOG\_Deinit@{CONSOLELOG\_Deinit}}
\index{CONSOLELOG\_Deinit@{CONSOLELOG\_Deinit}!record.c@{record.c}}
\doxysubsubsection{\texorpdfstring{CONSOLELOG\_Deinit()}{CONSOLELOG\_Deinit()}}
{\footnotesize\ttfamily \label{record_8c_a310ec37130ed3dad88f57c14e72a3ed7} 
\mbox{\hyperlink{error_8h_aeaf3178f631e362a9238a50fcdcaa039}{error\+\_\+t}} CONSOLELOG\+\_\+\+Deinit (\begin{DoxyParamCaption}\item[{void}]{}{}\end{DoxyParamCaption})}

De-\/\+Initializes The Recording System and Un-\/\+Mounts The File System. 

\begin{DoxyReturn}{Returns}
\doxylink{error_8h_aeaf3178f631e362a9238a50fcdcaa039}{error\+\_\+t} Returns 0 on Success, Otherwise E\+\_\+\+FAULT. 
\end{DoxyReturn}
\Hypertarget{record_8c_ae36046c53443afa593218c41f4b834fa}\index{record.c@{record.c}!CONSOLELOG\_Flush@{CONSOLELOG\_Flush}}
\index{CONSOLELOG\_Flush@{CONSOLELOG\_Flush}!record.c@{record.c}}
\doxysubsubsection{\texorpdfstring{CONSOLELOG\_Flush()}{CONSOLELOG\_Flush()}}
{\footnotesize\ttfamily \label{record_8c_ae36046c53443afa593218c41f4b834fa} 
\mbox{\hyperlink{error_8h_aeaf3178f631e362a9238a50fcdcaa039}{error\+\_\+t}} CONSOLELOG\+\_\+\+Flush (\begin{DoxyParamCaption}\item[{void}]{}{}\end{DoxyParamCaption})}

Flushes Collected Data To The File If No Other Data Have Been Received By The Time Specified By TIMEOUT Macro. 

If The Data Does Not Arrive By The Time Specified By The TIMEOUT Macro, Then This Function Flushes All The Data So Far Stored In The DMA Buffer, Saves It To a File on The Physical Media and Closes The File.

\begin{DoxyReturn}{Returns}
\doxylink{error_8h_aeaf3178f631e362a9238a50fcdcaa039}{error\+\_\+t} Returns 0 on Success, Otherwise Returns a Non-\/\+Zero Value. 
\end{DoxyReturn}
ADMA Error Status (ADMA\+\_\+\+ERR\+\_\+\+STATUS) 3 bit -\/\texorpdfstring{$>$}{>} ADMA Descriptor Error 2 bit -\/\texorpdfstring{$>$}{>} ADMA Length Mismatch Error 1-\/0 bit -\/\texorpdfstring{$>$}{>} ADMA Error State (When ADMA Error Occurred) Field Indicates The State of The ADMA When An Error Has Occurred During An ADMA Data Transfer.\Hypertarget{record_8c_af54d270ec7ba86c38b2903c41eca3676}\index{record.c@{record.c}!CONSOLELOG\_GetFlushCompleted@{CONSOLELOG\_GetFlushCompleted}}
\index{CONSOLELOG\_GetFlushCompleted@{CONSOLELOG\_GetFlushCompleted}!record.c@{record.c}}
\doxysubsubsection{\texorpdfstring{CONSOLELOG\_GetFlushCompleted()}{CONSOLELOG\_GetFlushCompleted()}}
{\footnotesize\ttfamily \label{record_8c_af54d270ec7ba86c38b2903c41eca3676} 
bool CONSOLELOG\+\_\+\+Get\+Flush\+Completed (\begin{DoxyParamCaption}\item[{void}]{}{}\end{DoxyParamCaption})}

Returns If Flush Was Completed or Not. 

\begin{DoxyReturn}{Returns}
If Recording Is Ongoing That Return False. 
\end{DoxyReturn}
\Hypertarget{record_8c_a68675110803994cd2f323d7b5ec22204}\index{record.c@{record.c}!CONSOLELOG\_GetFreeSpaceMB@{CONSOLELOG\_GetFreeSpaceMB}}
\index{CONSOLELOG\_GetFreeSpaceMB@{CONSOLELOG\_GetFreeSpaceMB}!record.c@{record.c}}
\doxysubsubsection{\texorpdfstring{CONSOLELOG\_GetFreeSpaceMB()}{CONSOLELOG\_GetFreeSpaceMB()}}
{\footnotesize\ttfamily \label{record_8c_a68675110803994cd2f323d7b5ec22204} 
uint32\+\_\+t CONSOLELOG\+\_\+\+Get\+Free\+Space\+MB (\begin{DoxyParamCaption}\item[{void}]{}{}\end{DoxyParamCaption})}

Gets Free Space on SD Card. 

\begin{DoxyReturn}{Returns}
Returns Free Space on SD Card. 
\end{DoxyReturn}
\Hypertarget{record_8c_a956fc952a186ae09ce21409b7354cde7}\index{record.c@{record.c}!CONSOLELOG\_GetTransferedBytes@{CONSOLELOG\_GetTransferedBytes}}
\index{CONSOLELOG\_GetTransferedBytes@{CONSOLELOG\_GetTransferedBytes}!record.c@{record.c}}
\doxysubsubsection{\texorpdfstring{CONSOLELOG\_GetTransferedBytes()}{CONSOLELOG\_GetTransferedBytes()}}
{\footnotesize\ttfamily \label{record_8c_a956fc952a186ae09ce21409b7354cde7} 
uint32\+\_\+t CONSOLELOG\+\_\+\+Get\+Transfered\+Bytes (\begin{DoxyParamCaption}\item[{void}]{}{}\end{DoxyParamCaption})}

Returns Currently Received Bytes Between LED Blinking. 

\begin{DoxyReturn}{Returns}
uint32\+\_\+t Received Bytes Between LED Blinking. 
\end{DoxyReturn}
\Hypertarget{record_8c_a7c874f2c9b56aa801cf2bee5565975f1}\index{record.c@{record.c}!CONSOLELOG\_Init@{CONSOLELOG\_Init}}
\index{CONSOLELOG\_Init@{CONSOLELOG\_Init}!record.c@{record.c}}
\doxysubsubsection{\texorpdfstring{CONSOLELOG\_Init()}{CONSOLELOG\_Init()}}
{\footnotesize\ttfamily \label{record_8c_a7c874f2c9b56aa801cf2bee5565975f1} 
\mbox{\hyperlink{error_8h_aeaf3178f631e362a9238a50fcdcaa039}{error\+\_\+t}} CONSOLELOG\+\_\+\+Init (\begin{DoxyParamCaption}\item[{void}]{}{}\end{DoxyParamCaption})}

Initializes The Recording System and Mounts The File System. 

This Function Performs the Initialization of The Recording System, Which includes\+:
\begin{DoxyItemize}
\item Setting Default Configuration Parameters.
\item Mounting the File System on The Logical Disk.
\item Optionally Setting Up The Current Working Drive.
\item Formatting The File System If It is Not Found (If Formatting is Enabled).
\end{DoxyItemize}

\begin{DoxyReturn}{Returns}
\doxylink{error_8h_aeaf3178f631e362a9238a50fcdcaa039}{error\+\_\+t} Returns ERROR\+\_\+\+NONE on Success, Otherwise ERROR\+\_\+\+FILESYSTEM. 
\end{DoxyReturn}
\Hypertarget{record_8c_a91b1773f5158d67d12e9c6d40394b841}\index{record.c@{record.c}!CONSOLELOG\_PowerLossFlush@{CONSOLELOG\_PowerLossFlush}}
\index{CONSOLELOG\_PowerLossFlush@{CONSOLELOG\_PowerLossFlush}!record.c@{record.c}}
\doxysubsubsection{\texorpdfstring{CONSOLELOG\_PowerLossFlush()}{CONSOLELOG\_PowerLossFlush()}}
{\footnotesize\ttfamily \label{record_8c_a91b1773f5158d67d12e9c6d40394b841} 
\mbox{\hyperlink{error_8h_aeaf3178f631e362a9238a50fcdcaa039}{error\+\_\+t}} CONSOLELOG\+\_\+\+Power\+Loss\+Flush (\begin{DoxyParamCaption}\item[{void}]{}{}\end{DoxyParamCaption})}

Flushes Collected Data To The File If Power Loss Was Detected. 

If Power Loss Was Detected, Then This Function Flushes All The Data So Far Stored In The DMA Buffer, Saves It To a File on The Physical Media and Closes The File.

\begin{DoxyReturn}{Returns}
\doxylink{error_8h_aeaf3178f631e362a9238a50fcdcaa039}{error\+\_\+t} Returns 0 on Success, Otherwise Returns a Non-\/\+Zero Value. 
\end{DoxyReturn}
ADMA Error Status (ADMA\+\_\+\+ERR\+\_\+\+STATUS) 3 bit -\/\texorpdfstring{$>$}{>} ADMA Descriptor Error 2 bit -\/\texorpdfstring{$>$}{>} ADMA Length Mismatch Error 1-\/0 bit -\/\texorpdfstring{$>$}{>} ADMA Error State (When ADMA Error Occurred) Field Indicates The State of The ADMA When An Error Has Occurred During An ADMA Data Transfer.\Hypertarget{record_8c_aeb7fb616b1f69f6cf4903a6058da06df}\index{record.c@{record.c}!CONSOLELOG\_ProccessConfigFile@{CONSOLELOG\_ProccessConfigFile}}
\index{CONSOLELOG\_ProccessConfigFile@{CONSOLELOG\_ProccessConfigFile}!record.c@{record.c}}
\doxysubsubsection{\texorpdfstring{CONSOLELOG\_ProccessConfigFile()}{CONSOLELOG\_ProccessConfigFile()}}
{\footnotesize\ttfamily \label{record_8c_aeb7fb616b1f69f6cf4903a6058da06df} 
\mbox{\hyperlink{error_8h_aeaf3178f631e362a9238a50fcdcaa039}{error\+\_\+t}} CONSOLELOG\+\_\+\+Proccess\+Config\+File (\begin{DoxyParamCaption}\item[{const char \texorpdfstring{$\ast$}{*}}]{content}{}\end{DoxyParamCaption})}

Processes The Content of The Configuration File To Extract and Validate The Baudrate. 

\begin{DoxyParams}[1]{Parameters}
\mbox{\texttt{ in}}  & {\em content} & Content The Content of The Configuration File as a Null-\/\+Terminated String.\\
\hline
\end{DoxyParams}
\begin{DoxyReturn}{Returns}
\doxylink{error_8h_aeaf3178f631e362a9238a50fcdcaa039}{error\+\_\+t} Returns 0 If Configuration File Is Correctly Processed, Otherwise Returns E\+\_\+\+FAULT. 
\end{DoxyReturn}
\Hypertarget{record_8c_af2718c8ac24b83f237cbd1dc970af06d}\index{record.c@{record.c}!CONSOLELOG\_ReadConfig@{CONSOLELOG\_ReadConfig}}
\index{CONSOLELOG\_ReadConfig@{CONSOLELOG\_ReadConfig}!record.c@{record.c}}
\doxysubsubsection{\texorpdfstring{CONSOLELOG\_ReadConfig()}{CONSOLELOG\_ReadConfig()}}
{\footnotesize\ttfamily \label{record_8c_af2718c8ac24b83f237cbd1dc970af06d} 
\mbox{\hyperlink{error_8h_aeaf3178f631e362a9238a50fcdcaa039}{error\+\_\+t}} CONSOLELOG\+\_\+\+Read\+Config (\begin{DoxyParamCaption}\item[{void}]{}{}\end{DoxyParamCaption})}

Reads and Processes The Configuration File From The Root directory. 

This Function Scans The Root Directory For a Configuration File, If The File is Found Reads its Contents Into g\+\_\+config Buffer.

\begin{DoxyReturn}{Returns}
\doxylink{error_8h_aeaf3178f631e362a9238a50fcdcaa039}{error\+\_\+t} Returns 0 If Configuration File Is Correctly Processed, Otherwise Returns E\+\_\+\+FAULT. 
\end{DoxyReturn}
\Hypertarget{record_8c_a79da7903033034cac5a75923611657f6}\index{record.c@{record.c}!CONSOLELOG\_Recording@{CONSOLELOG\_Recording}}
\index{CONSOLELOG\_Recording@{CONSOLELOG\_Recording}!record.c@{record.c}}
\doxysubsubsection{\texorpdfstring{CONSOLELOG\_Recording()}{CONSOLELOG\_Recording()}}
{\footnotesize\ttfamily \label{record_8c_a79da7903033034cac5a75923611657f6} 
\mbox{\hyperlink{error_8h_aeaf3178f631e362a9238a50fcdcaa039}{error\+\_\+t}} CONSOLELOG\+\_\+\+Recording (\begin{DoxyParamCaption}\item[{uint32\+\_\+t}]{file\+\_\+size}{}\end{DoxyParamCaption})}

Starts The Recording Process by Initializing the File System, Creating a Directory, and Writing to a File. 

Function Uses {\ttfamily CONSOLELOG\+\_\+\+Init} To Initialize The Recording System.

\begin{DoxyReturn}{Returns}
\doxylink{error_8h_aeaf3178f631e362a9238a50fcdcaa039}{error\+\_\+t} Returns 0 on Success, Otherwise Returns a Non-\/\+Zero Value. 
\end{DoxyReturn}
ADMA Error Status (ADMA\+\_\+\+ERR\+\_\+\+STATUS) 3 bit -\/\texorpdfstring{$>$}{>} ADMA Descriptor Error 2 bit -\/\texorpdfstring{$>$}{>} ADMA Length Mismatch Error 1-\/0 bit -\/\texorpdfstring{$>$}{>} ADMA Error State (When ADMA Error Occurred) Field Indicates The State of The ADMA When An Error Has Occurred During An ADMA Data Transfer.\Hypertarget{record_8c_af58b536abfd30f77213f4ecaf2ac52f5}\index{record.c@{record.c}!get\_fattime@{get\_fattime}}
\index{get\_fattime@{get\_fattime}!record.c@{record.c}}
\doxysubsubsection{\texorpdfstring{get\_fattime()}{get\_fattime()}}
{\footnotesize\ttfamily \label{record_8c_af58b536abfd30f77213f4ecaf2ac52f5} 
DWORD get\+\_\+fattime (\begin{DoxyParamCaption}\item[{void}]{}{}\end{DoxyParamCaption})}

MISRA Deviation\+: Rule 10.\+8 Suppress\+: Conversion From Smaller Unsigned Integer Types to a Wider Unsigned Type. Justification\+: The Cast From \textquotesingle{}Uint8\+\_\+t\textquotesingle{} and \textquotesingle{}Uint16\+\_\+t\textquotesingle{} to \textquotesingle{}Uint32\+\_\+t\textquotesingle{} is Intentional and Safe in This Context. The Values are Combined Using Bitwise OR Into a FAT Time Stamp Format That Expects 32-\/Bit Result. All Input Ranges are Within Limits.\Hypertarget{record_8c_aac632a55c01036580b0f0f2521de688b}\index{record.c@{record.c}!LP\_FLEXCOMM3\_IRQHandler@{LP\_FLEXCOMM3\_IRQHandler}}
\index{LP\_FLEXCOMM3\_IRQHandler@{LP\_FLEXCOMM3\_IRQHandler}!record.c@{record.c}}
\doxysubsubsection{\texorpdfstring{LP\_FLEXCOMM3\_IRQHandler()}{LP\_FLEXCOMM3\_IRQHandler()}}
{\footnotesize\ttfamily \label{record_8c_aac632a55c01036580b0f0f2521de688b} 
void LP\+\_\+\+FLEXCOMM3\+\_\+\+IRQHandler (\begin{DoxyParamCaption}\item[{void}]{}{}\end{DoxyParamCaption})}

LPUART3 IRQ Handler.
