Doly02/nxp-mcxn947-datalogger/application/doc/latex/task__switching_8h_source.tex

\doxysection{task\+\_\+switching.\+h}
\hypertarget{task__switching_8h_source}{}\label{task__switching_8h_source}\index{include/task\_switching.h@{include/task\_switching.h}}
\mbox{\hyperlink{task__switching_8h}{Go to the documentation of this file.}}
\begin{DoxyCode}{0}
\DoxyCodeLine{00001\ \textcolor{comment}{/******************************}}
\DoxyCodeLine{00002\ \textcolor{comment}{\ *\ \ Project:\ \ \ \ \ \ \ \ NXP\ MCXN947\ Datalogger}}
\DoxyCodeLine{00003\ \textcolor{comment}{\ *\ \ File\ Name:\ \ \ \ \ \ task\_switching.c}}
\DoxyCodeLine{00004\ \textcolor{comment}{\ *\ \ Author:\ \ \ \ \ \ \ \ \ Tomas\ Dolak}}
\DoxyCodeLine{00005\ \textcolor{comment}{\ *\ \ Date:\ \ \ \ \ \ \ \ \ \ \ 14.09.2024}}
\DoxyCodeLine{00006\ \textcolor{comment}{\ *\ \ Description:\ \ \ \ Includes\ Implementation\ of\ Task\ Switching\ (Record\ /\ USB\ Mass\ Storage).}}
\DoxyCodeLine{00007\ \textcolor{comment}{\ *}}
\DoxyCodeLine{00008\ \textcolor{comment}{\ *\ ****************************/}}
\DoxyCodeLine{00009\ }
\DoxyCodeLine{00010\ \textcolor{comment}{/******************************}}
\DoxyCodeLine{00011\ \textcolor{comment}{\ *\ \ @package\ \ \ \ \ \ \ \ NXP\ MCXN947\ Datalogger}}
\DoxyCodeLine{00012\ \textcolor{comment}{\ *\ \ @file\ \ \ \ \ \ \ \ \ \ \ task\_switching.c}}
\DoxyCodeLine{00013\ \textcolor{comment}{\ *\ \ @author\ \ \ \ \ \ \ \ \ Tomas\ Dolak}}
\DoxyCodeLine{00014\ \textcolor{comment}{\ *\ \ @date\ \ \ \ \ \ \ \ \ \ \ 14.09.2024}}
\DoxyCodeLine{00015\ \textcolor{comment}{\ *\ \ @brief\ \ \ \ \ \ \ \ \ \ Includes\ Implementation\ of\ Task\ Switching\ (Record\ /\ USB\ Mass\ Storage).}}
\DoxyCodeLine{00016\ \textcolor{comment}{\ *\ ****************************/}}
\DoxyCodeLine{00017\ }
\DoxyCodeLine{00018\ \textcolor{preprocessor}{\#ifndef\ TASK\_SWITCHING\_H\_}}
\DoxyCodeLine{00019\ \textcolor{preprocessor}{\#define\ TASK\_SWITCHING\_H\_}}
\DoxyCodeLine{00020\ }
\DoxyCodeLine{00021\ \textcolor{comment}{/*******************************************************************************}}
\DoxyCodeLine{00022\ \textcolor{comment}{\ *\ Includes}}
\DoxyCodeLine{00023\ \textcolor{comment}{\ ******************************************************************************/}}
\DoxyCodeLine{00024\ \textcolor{preprocessor}{\#include\ "{}usb\_device\_dci.h"{}}}
\DoxyCodeLine{00025\ }
\DoxyCodeLine{00026\ \textcolor{comment}{/*******************************************************************************}}
\DoxyCodeLine{00027\ \textcolor{comment}{\ *\ Global\ Variables}}
\DoxyCodeLine{00028\ \textcolor{comment}{\ ******************************************************************************/}}
\DoxyCodeLine{00032\ \textcolor{keyword}{extern}\ usb\_msc\_struct\_t\ \mbox{\hyperlink{task__switching_8h_ae3a33b5a19fe04eeba3ebf4259f74625}{g\_msc}};}
\DoxyCodeLine{00033\ \textcolor{comment}{/*******************************************************************************}}
\DoxyCodeLine{00034\ \textcolor{comment}{\ *\ Prototypes}}
\DoxyCodeLine{00035\ \textcolor{comment}{\ ******************************************************************************/}}
\DoxyCodeLine{00043\ usb\_device\_notification\_t\ \mbox{\hyperlink{task__switching_8h_ab4bb1b4063898f52aa390037fc37db81}{USB\_State}}(usb\_device\_struct\_t\ *pDeviceHandle);}
\DoxyCodeLine{00044\ }
\DoxyCodeLine{00045\ }
\DoxyCodeLine{00046\ \textcolor{preprocessor}{\#endif\ }\textcolor{comment}{/*\ TASK\_SWITCHING\_H\_\ */}\textcolor{preprocessor}{}}

\end{DoxyCode}
