Doly02/nxp-mcxn947-datalogger/application/doc/latex/topics.tex

\doxysection{Topics}
Here is a list of all topics with brief descriptions\+:\begin{DoxyCompactList}
\item \contentsline{section}{Task Management}{\pageref{group___task_management}}{}
\item \contentsline{section}{Buffers and Recording Management}{\pageref{group___recording}}{}
\item \contentsline{section}{Management}{\pageref{group___u_a_r_t}}{}
\item \contentsline{section}{DS3231 Real-\/\+Time Clock Driver}{\pageref{group___r_t_c}}{}
\end{DoxyCompactList}
