Doly02/nxp-mcxn947-datalogger/misc/leds.jpg

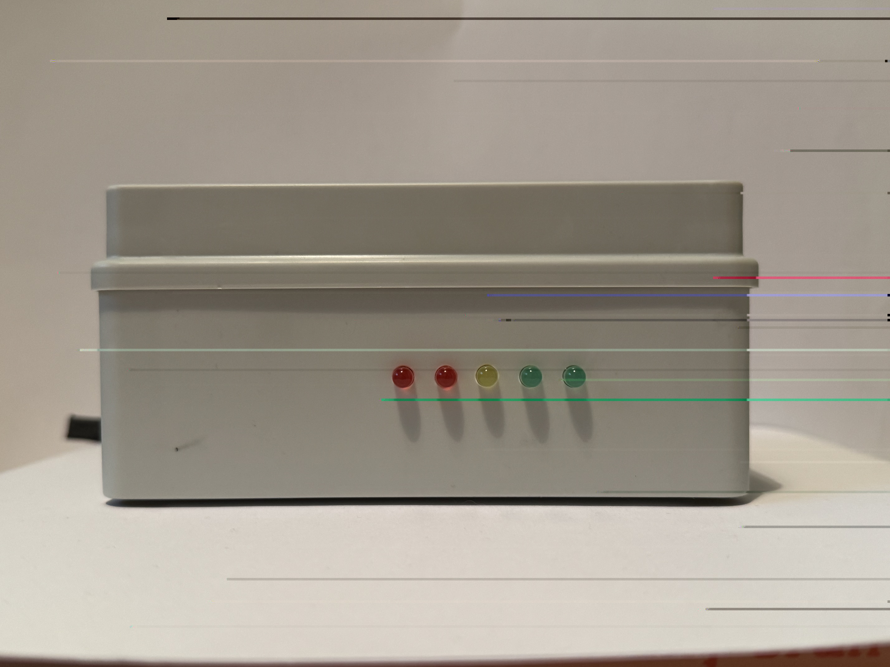
misc/leds.jpg
