Doly02/nxp-mcxn947-datalogger/misc/leds_after_flush.jpg

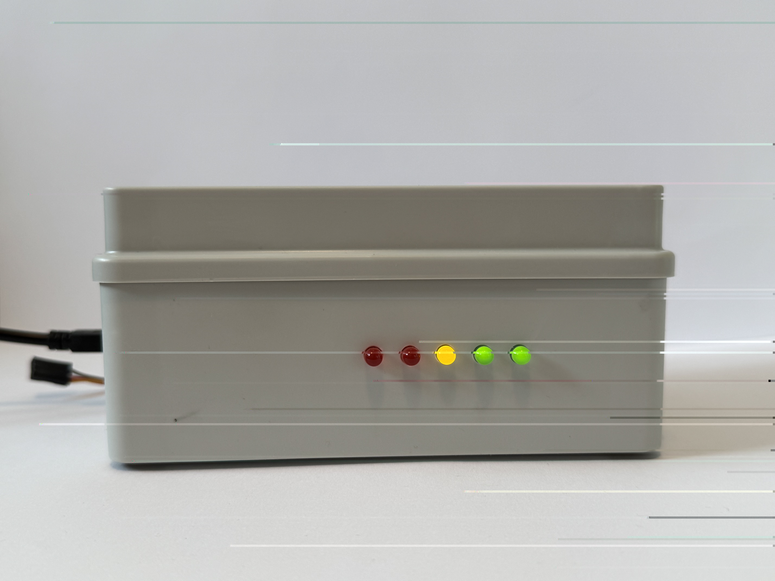
misc/leds_after_flush.jpg
