Doly02/nxp-mcxn947-datalogger/misc/leds_backup_power.jpg

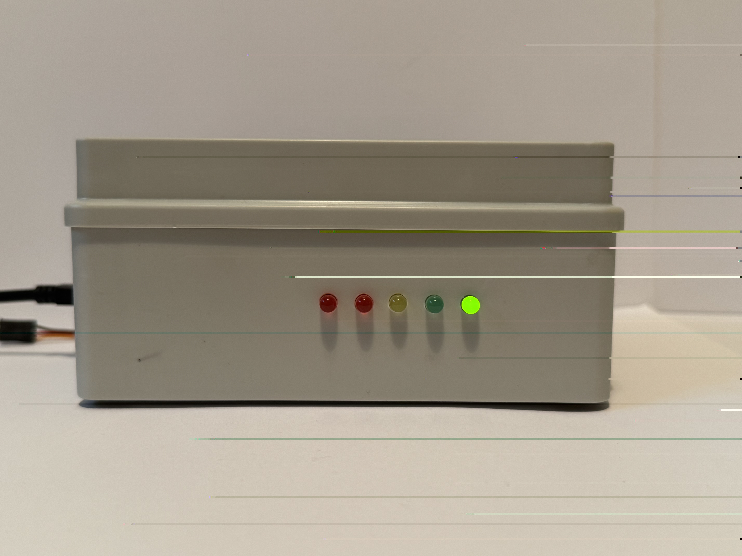
misc/leds_backup_power.jpg
