Doly02/nxp-mcxn947-datalogger/application/drivers/rtc_ds3231.c

/*
 *		Author: 		Tomas Dolak
 * 		File Name:		rtc_ds3231.c
 *      Description:	RTC DS3231 Driver.
 *		Created on: 	Aug 7, 2024
 *
 *		@author			Tomas Dolak
 * 		@brief			RTC DS3231 Driver.
 * 		@filename		rtc_ds3231.c
 */

/*******************************************************************************
 * Includes
 ******************************************************************************/
#include "rtc_ds3231.h"
/*******************************************************************************
 * Definitions
 ******************************************************************************/
/**
 * @brief Length of I2C Rx Buffer.
 */
#define I2C_DATA_LENGTH            	(2) /* MAX is 256 */

/*
 * @brief Other Definitions.
 */

/*
 * @brief First Byte.
 */
#define BYTE_1						(0U)

/*
 * @brief Seconds Byte.
 */
#define BYTE_2						(1U)

/*
 * @brief 	Returns The State of Internal Oscillator of DS3231.
 * @details OK / Oscillator Has Been Stop.
 */
#define CLK_STATE(x)				(uint8_t)((x >> 7) & 0x1)

/*******************************************************************************
 * Global Variables.
 ******************************************************************************/
/**
 * @brief	Reception Buffer.
 * @details	Must Be In Non-Cacheable Memory Due To Usage of DMA.
 */
AT_NONCACHEABLE_SECTION(uint8_t g_aRxBuff[I2C_DATA_LENGTH]);

/**
 * @brief	Transmission Buffer.
 * @details	Must Be In Non-Cacheable Memory Due To Usage of DMA.
 */
AT_NONCACHEABLE_SECTION(uint8_t gTxBuff[I2C_DATA_LENGTH]);

/**
 * @brief	eDMA Driver Handle Used For Non-Blocking DMA Transfer.
 */
AT_NONCACHEABLE_SECTION(lpi2c_master_edma_handle_t gEdmaHandle);

/**
 * @brief	Tx eDMA Handle.
 */
edma_handle_t gEdmaTxHandle;

/**
 * @brief	Rx eDMA Handle.
 */
edma_handle_t gEdmaRxHandle;

/**
 * @brief	Flag Indicating Whether The Transfer Has Finished.
 */
volatile bool gCompletionFlag 	= false;

/**
 * @brief   Transfer Descriptor for I2C Communication.
 * @details Used to Configure and Execute Data Transfer Operations With The DS3231 via LPI2C using EDMA.
 */
lpi2c_master_transfer_t xfer 	= {0};
/*******************************************************************************
 * Callback Functions
 ******************************************************************************/
static void lpi2c_callback(LPI2C_Type *base, lpi2c_master_edma_handle_t *handle, status_t status, void *userData)
{
    /* Signal transfer success when received success status. */
	if (kStatus_Success == status)
    {
    	gCompletionFlag = true;
    }
}
/*******************************************************************************
 * Functions
 ******************************************************************************/
uint8_t RTC_Init(void)
{
    lpi2c_master_config_t masterCfg;
    edma_config_t userCfg;
    status_t retVal = kStatus_Fail;

    /**
     * enableRoundRobinArbitration = false;
     * enableHaltOnError = true;
     * enableContinuousLinkMode = false;
     * enableDebugMode = false;
     **/
    EDMA_GetDefaultConfig(&userCfg);
    EDMA_Init(DMA0, &userCfg);

    LPI2C_MasterGetDefaultConfig(&masterCfg);
    masterCfg.baudRate_Hz = I2C_BAUDRATE;

    /* Initialize The LPI2C Master */
    LPI2C_MasterInit(I2C_MASTER, &masterCfg, CLOCK_GetLPFlexCommClkFreq(2u));

    /* Create The EDMA Channel Handles */
    EDMA_CreateHandle(&gEdmaTxHandle, DMA0, LPI2C_TX_DMA_CHANNEL);
    EDMA_CreateHandle(&gEdmaRxHandle, DMA0, LPI2C_RX_DMA_CHANNEL);
    EDMA_SetChannelMux(DMA0, LPI2C_TX_DMA_CHANNEL, LPI2C_TX_CHANNEL);
    EDMA_SetChannelMux(DMA0, LPI2C_RX_DMA_CHANNEL, LPI2C_RX_EDMA_CHANNEL);

    /* Create LPI2C Master DMA Driver Handle */
    LPI2C_MasterCreateEDMAHandle(I2C_MASTER, &gEdmaHandle, &gEdmaRxHandle, &gEdmaTxHandle,
                                 lpi2c_callback, NULL);

	/* Disable Alarms */
	RTC_CtrlAlarm1(ALARM_DISABLED);
	RTC_CtrlAlarm2(ALARM_DISABLED);
	RTC_ClearFlagAlarm1();
	RTC_ClearFlagAlarm2();

	/* Set Interrupt Mode */
	RTC_SetInterruptMode(ALARM_INTERRUPT);

	return APP_SUCCESS;

}

void RTC_Deinit(void)
{
	/* Abort Tx & Rx */
    EDMA_AbortTransfer(&gEdmaTxHandle);
    EDMA_AbortTransfer(&gEdmaRxHandle);

    /* De-Initialization of I2C */
    LPI2C_MasterDeinit(I2C_MASTER);

    /* De-Initialization of DMA */
    EDMA_Deinit(DMA0);

    CLOCK_EnableClock(kCLOCK_Port4);

    /*De-Inicialization of Pins Are Not Handled By The Driver, It's Board Specific */
}

/*
 * @brief General Functions.
 */
static uint8_t RTC_ConvertToBCD(uint8_t dec)
{
	/* BCD Is Not Defined For Numbers Greater Then 99 */
	 assert(dec < 99U);

	 return (dec % 10 + ((dec / 10) << 4));
}

static uint8_t RTC_ConvertToDEC(uint8_t bcd)
{
	return (((bcd & 0xf0) >> 4) * 10) + (bcd & 0x0f);
}

RTC_osc_state_t RTC_GetState(void)
{
	uint8_t bOscState = 0xFFu;		//<! Oscillator State
	bOscState = RTC_Read(DS3231_REG_STATUS);
	bOscState = ((bOscState >> 7) & 0xFFu);

	if (0x01u == bOscState)
	{
		/*
		 * A logic 1 in this bit indicates that the oscillator either is stopped or
		 * was stopped for some period and may be used to judge
		 * the validity of the time-keeping data.
		 *
		 * This bit is set to logic 1 any time that the oscillator stops.
		 * The following are examples of conditions that can cause the OSF bit to be set:
		 *
		 * 1) The first time power is applied.
		 * 2) The voltages present on both VCC and VBAT are insufficient to support oscillation.
		 * 3) The EOSC bit is turned off in battery-backed mode.
		 * 4) External influences on the crystal (i.e., noise, leakage, etc.).
		 *
		 * This bit remains at logic 1 until written to logic 0.
		 */
		return OSC_INTERRUPTED;
	}
	else
		return OSC_OK;
}

void RTC_SetOscState(RTC_osc_state_t state)
{
	if (OSC_OK == state)
	{
		// Clear The Flag
		// Set The Last Bit Of The Register To 0 By And With 127 (01111111b)
		RTC_Write(DS3231_REG_STATUS, ( 0x7Fu & RTC_Read(DS3231_REG_STATUS)));
	}
	else if (OSC_INTERRUPTED == state)
	{
		RTC_Write(DS3231_REG_STATUS, ( 0x80u | RTC_Read(DS3231_REG_STATUS)));
	}
	else
	{
		; // MISRA Compliance :)
	}
}



/*
 * @brief RTC Specific Functions.
 */
uint8_t RTC_Write(uint8_t regAddress, uint8_t val)
{
	gTxBuff[BYTE_1] = regAddress;
	gTxBuff[BYTE_2] = val;
	uint8_t retVal 	= 1;

    xfer.slaveAddress   = DS3231_ADDR_I2C;				/* Slave Address			*/
    xfer.direction      = kLPI2C_Write;					/* Direction (Read/Write)	*/
    xfer.subaddressSize = 0;							/* Sub-Address Size 		*/
    xfer.data           = gTxBuff;						/* Transmitted Data			*/
    xfer.dataSize       = 2;							/* Size of Transmitted Data	*/
    xfer.flags          = kLPI2C_TransferDefaultFlag;	/* Flags (e.g. Stop Flag) 	*/

    /* Send master non-blocking data to slave */
    retVal = LPI2C_MasterTransferEDMA(I2C_MASTER, &gEdmaHandle, &xfer);
    if ((uint8_t)kStatus_Success != retVal)
    {
        return (0xFF);
    }

    /*  Wait for transfer completed. */
	while (false == gCompletionFlag)
	{
		; /* Wait For Slave Complete */
	}
    gCompletionFlag = false;							// Reset
    return 0;
}

uint8_t RTC_Read(uint8_t regAddress)
{
	uint16_t rxVal		= 0;
	uint8_t retVal 		= 1;

    xfer.slaveAddress   = DS3231_ADDR_I2C;				/* Slave Address			*/
    xfer.direction      = kLPI2C_Write;					/* Direction (Read/Write)	*/
    xfer.subaddressSize = 0;							/* Sub-Address Size 		*/
    xfer.data           = &regAddress;					/* Transmitted Data			*/
    xfer.dataSize       = 1;							/* Size of Transmitted Data	*/
    xfer.flags          = kLPI2C_TransferDefaultFlag;	/* Flags (e.g. Stop Flag) 	*/
    /* Receive non-blocking data from slave */
    retVal = LPI2C_MasterTransferEDMA(I2C_MASTER, &gEdmaHandle, &xfer);
    if ((uint8_t)kStatus_Success != retVal)
    {
        return (0xFF);
    }

	while (false == gCompletionFlag)
	{
		; /* Wait For Slave Complete */
	}

    gCompletionFlag = false;							// Reset


	xfer.slaveAddress   = DS3231_ADDR_I2C;				/* Slave Address			*/
	xfer.direction      = kLPI2C_Read;					/* Direction (Read/Write)	*/
	xfer.subaddressSize = 0;							/* Sub-Address Size 		*/
	xfer.data           = g_aRxBuff;						/* Transmitted Data			*/
	xfer.dataSize       = 1;							/* Size of Transmitted Data	*/
	xfer.flags          = kLPI2C_TransferDefaultFlag;	/* Flags (e.g. Stop Flag) 	*/

    /* Receive non-blocking data from slave */
    retVal = LPI2C_MasterTransferEDMA(I2C_MASTER, &gEdmaHandle, &xfer);
    if ((uint8_t)kStatus_Success != retVal)
    {
        return (0xFF);
    }

	while (false == gCompletionFlag)
	{
		; /* Wait For Slave Complete */
	}

    gCompletionFlag = false;							// Reset

	rxVal = (g_aRxBuff[0]);
    return rxVal;
}


void RTC_SetTime(RTC_time_t *pTime)
{
	uint8_t ui8BcdNum = 0xFF;

	/* Set Seconds */
	ui8BcdNum = RTC_ConvertToBCD(pTime->sec);
	RTC_Write(DS3231_ADDR_SEC, ui8BcdNum);

	/* Set Minutes */
	RTC_Write(DS3231_ADDR_MIN, RTC_ConvertToBCD(pTime->min));

	/* Write Value of Hours Into RTC Register (In 24H Format) */
	ui8BcdNum = RTC_ConvertToBCD(pTime->hrs  & 0x3Fu);
	RTC_Write(DS3231_ADDR_HRS, ui8BcdNum);

	return;
}


void RTC_GetTime(RTC_time_t *pTime)
{
	uint8_t ui8Val;
	uint8_t ui8Format;

	ui8Val = RTC_Read(DS3231_ADDR_SEC);
	ui8Val = RTC_ConvertToDEC(ui8Val);
	pTime->sec = ui8Val;

	ui8Val = RTC_Read(DS3231_ADDR_MIN);
	ui8Val = RTC_ConvertToDEC(ui8Val);
	pTime->min = ui8Val;

	ui8Val = RTC_Read(DS3231_ADDR_HRS);
	/* Convert From Binary Coded Decimal */
	pTime->hrs = RTC_ConvertToDEC(ui8Val);		//<! Hours In 24H Format.

	return;
}

void RTC_SetDate(RTC_date_t *pDate)
{
	RTC_Write(DS3231_ADDR_DATE, RTC_ConvertToBCD(pDate->date));
	RTC_Write(DS3231_ADDR_DAY, RTC_ConvertToBCD(pDate->day));
	RTC_Write(DS3231_ADDR_MONTH, RTC_ConvertToBCD(pDate->month));
	RTC_Write(DS3231_ADDR_YEAR, RTC_ConvertToBCD(pDate->year));

	return;
}

void RTC_GetDate(RTC_date_t *pDate)
{
	uint8_t ui8RegVal = 0xFFu;
	ui8RegVal = RTC_Read(DS3231_ADDR_DATE);
	pDate->date = RTC_ConvertToDEC(ui8RegVal);

	ui8RegVal = RTC_Read(DS3231_ADDR_DAY);
	pDate->day = RTC_ConvertToDEC(ui8RegVal);

	ui8RegVal = RTC_Read(DS3231_ADDR_MONTH);
	pDate->month = RTC_ConvertToDEC(ui8RegVal);

	ui8RegVal = RTC_Read(DS3231_ADDR_YEAR);
	pDate->year = RTC_ConvertToDEC(ui8RegVal);

	return;
}
/*
 * -----------------------------------------------------------------------------------------
 */
void RTC_SetInterruptMode(RTC_interrupt_mode_t mode)
{
	uint8_t ctrl = RTC_Read(DS3231_REG_CTRL);
	RTC_Write(DS3231_REG_CTRL, (ctrl & 0xfb) | ((mode & 0x01) << DS3231_INTCN));
}

void RTC_CtrlAlarm1(uint8_t enable)
{
	uint8_t ctrl = RTC_Read(DS3231_REG_CTRL);
	RTC_Write(DS3231_REG_CTRL,(ctrl & 0xfe) | ((enable & 0x01) << DS3231_A1IE));
	RTC_SetInterruptMode(ALARM_INTERRUPT);

}
void RTC_ClearFlagAlarm1(void)
{
	uint8_t status = (RTC_Read(DS3231_REG_STATUS) & 0xfe);
	RTC_Write(DS3231_REG_STATUS, status & ~(0x01 << DS3231_A1F));
}

void RTC_CtrlAlarm2(uint8_t enable)
{
	uint8_t ctrl = RTC_Read(DS3231_REG_CTRL);
	RTC_Write(DS3231_REG_CTRL, (ctrl & 0xfd) | ((enable & 0x01) << DS3231_A2IE));
	RTC_SetInterruptMode(ALARM_INTERRUPT);
}

void RTC_ClearFlagAlarm2(void)
{
	uint8_t status = (RTC_Read(DS3231_REG_STATUS) & 0xfd);
	RTC_Write(DS3231_REG_STATUS, status & ~(0x01 << DS3231_A2F));
}

/*
 * -----------------------------------------------------------------------------------------
 */
void RTC_SetTimeDefault(RTC_time_t *pTime)
{
	pTime->format = TIM_CYCLE_24H;
	pTime->hrs = 10;
	pTime->min = 48;
	pTime->sec = 48;
}

void RTC_SetDateDefault(RTC_date_t *pDate)
{
	pDate->date = 4;
	pDate->month = 6;
	pDate->year = 2;
	pDate->day = FRIDAY;
}
