Doly02/nxp-mcxn947-datalogger/application/src/app_tasks.c

/******************************
 *  Project:        NXP MCXN947 Datalogger
 *  File Name:      tasks.c
 *  Author:         Tomas Dolak
 *  Date:           14.09.2024
 *  Description:    Includes Implementation of FreeRTOS Task.
 *
 * ****************************/

/******************************
 *  @package        NXP MCXN947 Datalogger
 *  @file           tasks.c
 *  @author         Tomas Dolak
 *  @date           14.09.2024
 *  @brief          Includes Implementation of FreeRTOS Task.
 * ****************************/

/*******************************************************************************
 * Includes
 ******************************************************************************/
#include "app_tasks.h"
#include "rtc_ds3231.h"
#include "mass_storage.h"

#include "task_switching.h"
#include "record.h"

/**
 * MISRA Deviation: Rule 21.10
 * Suppress: Use Of Banned Standard Header 'Time.h'.
 * Justification: 'time.h' Is Used For Generating Timestamps.
 */
/*lint -e829 */
#include <time.h>
/*lint +e829  */
/*******************************************************************************
 * Global Variables.
 ******************************************************************************/
/**
 * @defgroup 	TaskManagement Task Management
 * @brief 		Group Contains Task Management Variables and Metadata.
 * @{
 */

/*!
 * @brief	TCB (Task Control Block) - Meta-Data of IDLE Task.
 */
static StaticTask_t xIdleTaskTCB;
/*!
 * @brief 	Stack for Static Idle Task.
 */
static StackType_t uxIdleTaskStack[configMINIMAL_STACK_SIZE];

/*!
 * @brief	TCB (Task Control Block) - Meta-Data of Timer Task.
 */
static StaticTask_t xTimerTaskTCB;

/*!
 * @brief 	Stack for Static Timer Task.
 */
/**
 * MISRA Deviation Note:
 * Rule: MISRA 2012 Rule 10.4 [Required]
 * Suppress: Standard FreeRTOS Macro Cast To uint32_t
 * Justification: The macro 'configTIMER_TASK_STACK_DEPTH' is defined by the FreeRTOS kernel
 * configuration as an integer constant.
 */
/*lint -e9029 */
static StackType_t uxTimerTaskStack[configTIMER_TASK_STACK_DEPTH];
/*lint +e9029 */

/** @} */ // End of TaskManagement group

/*******************************************************************************
 * Implementation of Functions
 ******************************************************************************/


/*******************************************************************************
 * Implementation of Functions
 ******************************************************************************/

/*******************************************************************************
 * Implementation of Functions
 ******************************************************************************/

void msc_task(void *handle)
{
    while (true)
    {

    	/* Wait Here Till USB Is Attached */
    	(void)xSemaphoreTake(g_xSemMassStorage, portMAX_DELAY);

        /* Disable Recording & Close Current Record If It's Opened */
        UART_Disable();

#if (true == INFO_ENABLED)
        PRINTF("INFO: Disabled LPUART7\r\n");
#endif /* (true == INFO_ENABLED) */
        if (ERROR_NONE != CONSOLELOG_PowerLossFlush())
		{
        	LED_SignalError();
		}

        while (true)
        {
            MSC_DeviceMscAppTask();

            /* If USB Is Detached Then Switch To Record Task */
            if (USB_State(g_msc.deviceHandle) == kUSB_DeviceNotifyDetach)
            {
#if (true == INFO_ENABLED)
                PRINTF("INFO: MSC Task Ending - USB Detached\r\n");
#endif
                (void)xSemaphoreGive(g_xSemRecord);
                break;
            }

            vTaskDelay(pdMS_TO_TICKS(100));
        }
    }
}



void record_task(void *handle)
{
    error_t  retVal             = ERROR_UNKNOWN;
    uint32_t u32Baudrate        = 0UL;
    uint32_t u32FileSize        = 0UL;
    uint32_t u32CurrentBytes    = 0UL;
    uint32_t u32MaxBytes        = 0UL;
    uint32_t u32FreeSpaceSdCard = 0UL;
    uint32_t u32FreeSpaceLimit  = 0UL;
    edma_config_t edmaConfig 	= { 0U };

    /* Initialize SD Card and File System */
    USB_DeviceModeInit();

    /* Initialize DMA For I2C Communication With DS3231 */
	edmaConfig.enableRoundRobinArbitration 	= false;
	edmaConfig.enableHaltOnError 			= true;
	edmaConfig.enableMasterIdReplication 	= false;
	edmaConfig.enableDebugMode 				= false;
	edmaConfig.enableGlobalChannelLink 		= true;
	EDMA_Init(LPI2C_DMA_BASEADDR, &edmaConfig);


    (void)CLOCK_SetupClk16KClocking((uint32_t)((uint32_t)kCLOCK_Clk16KToVbat | (uint32_t)kCLOCK_Clk16KToMain));
    (void)TIME_InitIRTC();

    /* De-Inicialization of External RTC (After Initialization This RTC Is Not Needed */
	RTC_Deinit();
	LPI2C2_DeinitPins();

    retVal = CONSOLELOG_Init();
    if(ERROR_NONE != retVal)
	{
    	LED_SignalError();
		return;
	}

    USB_DeviceRun(g_msc.deviceHandle);
    USB_DeviceIsrEnable();

    if (CONSOLELOG_ReadConfig() != ERROR_NONE)
    {
        u32Baudrate = DEFAULT_BAUDRATE;
        u32FileSize = DEFAULT_MAX_FILESIZE;
    }
    else
    {
        u32Baudrate = PARSER_GetBaudrate();
        u32FileSize = PARSER_GetFileSize();
    }



    while (true)
    {

    	(void)xSemaphoreTake(g_xSemRecord, portMAX_DELAY);

		UART_Init(u32Baudrate);
		UART_Enable();

#if (true == INFO_ENABLED)
		PRINTF("INFO: UART Initialized for Record Mode\r\n");
#endif /* (true == INFO_ENABLED) */

        while (kUSB_DeviceNotifyAttach != USB_State(g_msc.deviceHandle))
        {
			if (ERROR_NONE != CONSOLELOG_Recording(u32FileSize))
			{
#if (CONTROL_LED_ENABLED == true)
				LED_SignalError();
#endif /* (CONTROL_LED_ENABLED == true) */
				ERR_HandleError();
			}

			if (ERROR_NONE != CONSOLELOG_Flush())
			{
#if (CONTROL_LED_ENABLED == true)
				LED_SignalError();
#endif /* (CONTROL_LED_ENABLED == true) */
				ERR_HandleError();
			}

#if (CONTROL_LED_ENABLED == true)
			u32CurrentBytes = CONSOLELOG_GetTransferedBytes();
			u32MaxBytes = PARSER_GetMaxBytes();
			if (u32CurrentBytes >= u32MaxBytes)
			{
				LED_SignalRecording();
				CONSOLELOG_ClearTransferedBytes();
				LED_ClearSignalFlush();
			}
#endif

#if (true == CONTROL_LED_ENABLED)
			u32FreeSpaceSdCard = CONSOLELOG_GetFreeSpaceMB();
			u32FreeSpaceLimit = PARSER_GetFreeSpaceLimitMB();

			if ((u32FreeSpaceSdCard <= u32FreeSpaceLimit) &&
				(0UL != u32FreeSpaceLimit))
			{
				LED_SignalLowMemory();
#if (true == DEBUG_ENABLED)
				PRINTF("DEBUG: Free Space: %d MB\r\n", u32FreeSpaceSdCard);
#endif /* (true == DEBUG_ENABLED) */
			}
#endif /* (true == CONTROL_LED_ENABLED) */

        }

		(void)xSemaphoreGive(g_xSemMassStorage);
    }
}


void vApplicationGetIdleTaskMemory(StaticTask_t **ppxIdleTaskTCBBuffer,
                                   StackType_t **ppxIdleTaskStackBuffer,
                                   uint32_t *pulIdleTaskStackSize)
{
    *ppxIdleTaskTCBBuffer = &xIdleTaskTCB;
    *ppxIdleTaskStackBuffer = uxIdleTaskStack;

    /**
     * MISRA Deviation: Rule 10.8 [Required]
     * Suppress: Conversion From Signed Macro To Unsigned Type.
     * Justification: 'ConfigMINIMAL_STACK_SIZE' Is Defined By FreeRTOS As A Signed Macro.
     * The Conversion To 'Uint32_t' Is Intentional And Safe In This Context.
     * Fixing The Definition is Not Possible.
     */
    /*lint -e9029 */
    *pulIdleTaskStackSize = (uint32_t)configMINIMAL_STACK_SIZE;
    /*lint +e9029 */
}

void vApplicationGetTimerTaskMemory(StaticTask_t **ppxTimerTaskTCBBuffer,
                                    StackType_t **ppxTimerTaskStackBuffer,
                                    uint32_t *pulTimerTaskStackSize)
{
    *ppxTimerTaskTCBBuffer = &xTimerTaskTCB;
    *ppxTimerTaskStackBuffer = uxTimerTaskStack;

    /**
     * MISRA Deviation: Rule 10.8 [Required]
     * Suppress: Conversion From Signed Macro To Unsigned Type.
     * Justification: 'configTIMER_TASK_STACK_DEPTH' Is Defined By FreeRTOS As A Signed Macro.
     * The Conversion To 'Uint32_t' Is Intentional And Safe In This Context.
     * Fixing The Definition is Not Possible.
     */
    /*lint -e9029 */
    *pulTimerTaskStackSize = (uint32_t)configTIMER_TASK_STACK_DEPTH;
    /*lint +e9029 */
}
